bemcgarvey/SAMduino/firmware/FullDemo/firmware/src/config/default/default.mhc/project.yml

files:
- generatedChecksum: F58DB2348A0FCE945652B285010E5F8A
  logicalPath: FreeRTOS/Source
  name: FreeRTOS_tasks.c
  physicalPath: ../../third_party/rtos/FreeRTOS/Source
  security: NON_SECURE
  type: SOURCE
  userChecksum: F58DB2348A0FCE945652B285010E5F8A
- generatedChecksum: 3C13720844166A5D97CF4EAD9DDB9FE2
  logicalPath: ''
  name: app.c
  physicalPath: ../..
  security: NON_SECURE
  type: SOURCE
  userChecksum: 3C13720844166A5D97CF4EAD9DDB9FE2
- generatedChecksum: 8ACE0DEBD82F6829438A4674565451FB
  logicalPath: FreeRTOS/Source
  name: croutine.c
  physicalPath: ../../third_party/rtos/FreeRTOS/Source
  security: NON_SECURE
  type: SOURCE
  userChecksum: 8ACE0DEBD82F6829438A4674565451FB
- generatedChecksum: EA052CFEAD3E59E304995DACA53CE9B6
  logicalPath: config/default/driver/sst26
  name: drv_sst26.c
  physicalPath: driver/sst26/src
  security: NON_SECURE
  type: SOURCE
  userChecksum: EA052CFEAD3E59E304995DACA53CE9B6
- generatedChecksum: 680300EC1B71F449C4265A35B9ECA1BF
  logicalPath: config/default/driver/usb/usbhsv1/src
  name: drv_usbhsv1.c
  physicalPath: driver/usb/usbhsv1/src
  security: NON_SECURE
  type: SOURCE
  userChecksum: 680300EC1B71F449C4265A35B9ECA1BF
- generatedChecksum: 33A4AF962D182E0E51963CD431EE5B25
  logicalPath: config/default/driver/usb/usbhsv1/src
  name: drv_usbhsv1_device.c
  physicalPath: driver/usb/usbhsv1/src
  security: NON_SECURE
  type: SOURCE
  userChecksum: 33A4AF962D182E0E51963CD431EE5B25
- generatedChecksum: B3B5445B14BD9B6A35F1C5B995C9BBF7
  logicalPath: FreeRTOS/Source
  name: event_groups.c
  physicalPath: ../../third_party/rtos/FreeRTOS/Source
  security: NON_SECURE
  type: SOURCE
  userChecksum: B3B5445B14BD9B6A35F1C5B995C9BBF7
- generatedChecksum: 6069C4FD56993BDA3B1FC223DD5BAA4A
  logicalPath: config/default
  name: exceptions.c
  physicalPath: ''
  security: NON_SECURE
  type: SOURCE
  userChecksum: 6069C4FD56993BDA3B1FC223DD5BAA4A
- generatedChecksum: B7DBFD6F500AAD4713403E985EB18EAE
  logicalPath: config/default
  name: freertos_hooks.c
  physicalPath: ''
  security: NON_SECURE
  type: SOURCE
  userChecksum: B7DBFD6F500AAD4713403E985EB18EAE
- generatedChecksum: 972E955D94A63BA89BF6ABD6AADB1023
  logicalPath: FreeRTOS/Source/portable/MemMang
  name: heap_1.c
  physicalPath: ../../third_party/rtos/FreeRTOS/Source/portable/MemMang
  security: NON_SECURE
  type: SOURCE
  userChecksum: 972E955D94A63BA89BF6ABD6AADB1023
- generatedChecksum: 76F34BFBB493FA46B344390C7CF3CD15
  logicalPath: config/default
  name: initialization.c
  physicalPath: ''
  security: NON_SECURE
  type: SOURCE
  userChecksum: AD14C167BFB01463832A4C5FFC92C627
- generatedChecksum: BDF1F360A3F8C5AD9AE4D64B657A1878
  logicalPath: config/default
  name: interrupts.c
  physicalPath: ''
  security: NON_SECURE
  type: SOURCE
  userChecksum: BDF1F360A3F8C5AD9AE4D64B657A1878
- generatedChecksum: 6513F2461B8F476B68CA73906086047F
  logicalPath: config/default
  name: libc_syscalls.c
  physicalPath: ''
  security: NON_SECURE
  type: SOURCE
  userChecksum: 6513F2461B8F476B68CA73906086047F
- generatedChecksum: 3FEE521CEF14928AE38E7FA9BF6D75E6
  logicalPath: FreeRTOS/Source
  name: list.c
  physicalPath: ../../third_party/rtos/FreeRTOS/Source
  security: NON_SECURE
  type: SOURCE
  userChecksum: 3FEE521CEF14928AE38E7FA9BF6D75E6
- generatedChecksum: null
  logicalPath: ''
  name: main.c
  physicalPath: ../..
  security: NON_SECURE
  type: SOURCE
  userChecksum: null
- generatedChecksum: 8FDD6248506F28B32C4F5FD9AA0D9C6F
  logicalPath: config/default/osal
  name: osal_freertos.c
  physicalPath: osal
  security: NON_SECURE
  type: SOURCE
  userChecksum: 8FDD6248506F28B32C4F5FD9AA0D9C6F
- generatedChecksum: 706B0D62C31518F05ECE479F341C0C4A
  logicalPath: config/default/peripheral/afec
  name: plib_afec0.c
  physicalPath: peripheral/afec
  security: NON_SECURE
  type: SOURCE
  userChecksum: 706B0D62C31518F05ECE479F341C0C4A
- generatedChecksum: CCAA3BBC352DB66DF3CFBB76D3ADD2E2
  logicalPath: config/default/peripheral/clk
  name: plib_clk.c
  physicalPath: peripheral/clk
  security: NON_SECURE
  type: SOURCE
  userChecksum: CCAA3BBC352DB66DF3CFBB76D3ADD2E2
- generatedChecksum: 0B346F78158581AC40B9AC5F314CCE8B
  logicalPath: config/default/peripheral/dacc
  name: plib_dacc.c
  physicalPath: peripheral/dacc
  security: NON_SECURE
  type: SOURCE
  userChecksum: 0B346F78158581AC40B9AC5F314CCE8B
- generatedChecksum: D23DF612DB8267EDD9F5F3A463A02DB2
  logicalPath: config/default/peripheral/efc
  name: plib_efc.c
  physicalPath: peripheral/efc
  security: NON_SECURE
  type: SOURCE
  userChecksum: D23DF612DB8267EDD9F5F3A463A02DB2
- generatedChecksum: ED0FB91129ED2FAB77A9B83BCA98BB56
  logicalPath: config/default/peripheral/mcan
  name: plib_mcan1.c
  physicalPath: peripheral/mcan
  security: NON_SECURE
  type: SOURCE
  userChecksum: 1BCA5DFF8679503FCB69D2AA16217BDE
- generatedChecksum: 491997C3DCC743A5F66EBE18F705C9AF
  logicalPath: config/default/peripheral/mpu
  name: plib_mpu.c
  physicalPath: peripheral/mpu
  security: NON_SECURE
  type: SOURCE
  userChecksum: 491997C3DCC743A5F66EBE18F705C9AF
- generatedChecksum: 37F79C56E4B0579F6756EA357A5D6681
  logicalPath: config/default/peripheral/nvic
  name: plib_nvic.c
  physicalPath: peripheral/nvic
  security: NON_SECURE
  type: SOURCE
  userChecksum: 2B41430E0F8341E7698B5F92560EFE35
- generatedChecksum: AECA335D842D380909F5F2B9B9303612
  logicalPath: config/default/peripheral/pio
  name: plib_pio.c
  physicalPath: peripheral/pio
  security: NON_SECURE
  type: SOURCE
  userChecksum: AECA335D842D380909F5F2B9B9303612
- generatedChecksum: D54BE86FE71C530355BA300B4662D361
  logicalPath: config/default/peripheral/pwm
  name: plib_pwm0.c
  physicalPath: peripheral/pwm
  security: NON_SECURE
  type: SOURCE
  userChecksum: D54BE86FE71C530355BA300B4662D361
- generatedChecksum: 164CDE8DEA8E52ED78CD9E179EDDE260
  logicalPath: config/default/peripheral/qspi
  name: plib_qspi.c
  physicalPath: peripheral/qspi
  security: NON_SECURE
  type: SOURCE
  userChecksum: 164CDE8DEA8E52ED78CD9E179EDDE260
- generatedChecksum: 68F6A46E5DB2303BD0B1DC03F3436C98
  logicalPath: config/default/peripheral/rtc
  name: plib_rtc.c
  physicalPath: peripheral/rtc
  security: NON_SECURE
  type: SOURCE
  userChecksum: 68F6A46E5DB2303BD0B1DC03F3436C98
- generatedChecksum: B09ED1072864A1FCF957C698795DD7BD
  logicalPath: config/default/peripheral/tc
  name: plib_tc0.c
  physicalPath: peripheral/tc
  security: NON_SECURE
  type: SOURCE
  userChecksum: B09ED1072864A1FCF957C698795DD7BD
- generatedChecksum: 037AFDA32620C47534016E979C15AF5C
  logicalPath: config/default/peripheral/tc
  name: plib_tc1.c
  physicalPath: peripheral/tc
  security: NON_SECURE
  type: SOURCE
  userChecksum: 037AFDA32620C47534016E979C15AF5C
- generatedChecksum: 1DE96220F35A04CB1742747EFEA865BD
  logicalPath: config/default/peripheral/trng
  name: plib_trng.c
  physicalPath: peripheral/trng
  security: NON_SECURE
  type: SOURCE
  userChecksum: 1DE96220F35A04CB1742747EFEA865BD
- generatedChecksum: AD9E5D8957ADDF3C5B579114051BE96B
  logicalPath: config/default/peripheral/twihs/master
  name: plib_twihs0_master.c
  physicalPath: peripheral/twihs/master
  security: NON_SECURE
  type: SOURCE
  userChecksum: AD9E5D8957ADDF3C5B579114051BE96B
- generatedChecksum: CBEC3B1A0CD099BE51536D94DED55A0F
  logicalPath: config/default/peripheral/uart
  name: plib_uart0.c
  physicalPath: peripheral/uart
  security: NON_SECURE
  type: SOURCE
  userChecksum: 4709090D31EC54B2A1883D1C04EC0574
- generatedChecksum: A44EAFDF7F180C2C05A0AE0AEB3FB80C
  logicalPath: FreeRTOS/Source/portable/GCC/SAM/CM7
  name: port.c
  physicalPath: ../../third_party/rtos/FreeRTOS/Source/portable/GCC/SAM/CM7
  security: NON_SECURE
  type: SOURCE
  userChecksum: A44EAFDF7F180C2C05A0AE0AEB3FB80C
- generatedChecksum: 09041728D74A4E3A32C7D4EAA96C4EE7
  logicalPath: FreeRTOS/Source
  name: queue.c
  physicalPath: ../../third_party/rtos/FreeRTOS/Source
  security: NON_SECURE
  type: SOURCE
  userChecksum: 09041728D74A4E3A32C7D4EAA96C4EE7
- generatedChecksum: F199C711F99DEF2498D1F664873F2B12
  logicalPath: config/default
  name: startup_xc32.c
  physicalPath: ''
  security: NON_SECURE
  type: SOURCE
  userChecksum: F199C711F99DEF2498D1F664873F2B12
- generatedChecksum: D6CF30BDCE1A813D9ACF3905EBD6A871
  logicalPath: FreeRTOS/Source
  name: stream_buffer.c
  physicalPath: ../../third_party/rtos/FreeRTOS/Source
  security: NON_SECURE
  type: SOURCE
  userChecksum: D6CF30BDCE1A813D9ACF3905EBD6A871
- generatedChecksum: 9063CE23C03357B7F90CA6887D4BCAF9
  logicalPath: config/default/system/cache
  name: sys_cache.c
  physicalPath: system/cache
  security: NON_SECURE
  type: SOURCE
  userChecksum: 9063CE23C03357B7F90CA6887D4BCAF9
- generatedChecksum: 02C3C1B519E59992810626BB6098CF56
  logicalPath: config/default/system/int
  name: sys_int.c
  physicalPath: system/int/src
  security: NON_SECURE
  type: SOURCE
  userChecksum: 02C3C1B519E59992810626BB6098CF56
- generatedChecksum: 83BDE663A1AAB20C9E52263F22E2ED3C
  logicalPath: config/default/system/time
  name: sys_time.c
  physicalPath: system/time/src
  security: NON_SECURE
  type: SOURCE
  userChecksum: 83BDE663A1AAB20C9E52263F22E2ED3C
- generatedChecksum: C0B55E4D4726999758344B4532A6EF5F
  logicalPath: config/default
  name: tasks.c
  physicalPath: ''
  security: NON_SECURE
  type: SOURCE
  userChecksum: 2D95749151AAFEBDD75F7073DBA08B05
- generatedChecksum: F1B86F6E1527FD59A8713B67564F2898
  logicalPath: FreeRTOS/Source
  name: timers.c
  physicalPath: ../../third_party/rtos/FreeRTOS/Source
  security: NON_SECURE
  type: SOURCE
  userChecksum: F1B86F6E1527FD59A8713B67564F2898
- generatedChecksum: BCCEF5B801FFD0CF22D0B454D2F25F1F
  logicalPath: config/default/usb/src
  name: usb_device.c
  physicalPath: usb/src
  security: NON_SECURE
  type: SOURCE
  userChecksum: BCCEF5B801FFD0CF22D0B454D2F25F1F
- generatedChecksum: B8D87B6533E2CE239E9EEB8486DF6996
  logicalPath: config/default/usb/src
  name: usb_device_hid.c
  physicalPath: usb/src
  security: NON_SECURE
  type: SOURCE
  userChecksum: B8D87B6533E2CE239E9EEB8486DF6996
- generatedChecksum: A4132D906937F33AE060B60BD472DB28
  logicalPath: config/default
  name: usb_device_init_data.c
  physicalPath: ''
  security: NON_SECURE
  type: SOURCE
  userChecksum: A4132D906937F33AE060B60BD472DB28
- generatedChecksum: A49786F231DE2706850DA13580EF4BB5
  logicalPath: config/default/stdio
  name: xc32_monitor.c
  physicalPath: stdio
  security: NON_SECURE
  type: SOURCE
  userChecksum: A49786F231DE2706850DA13580EF4BB5
- generatedChecksum: AF3A8D8AA610E7DFD3E38DDAC5E42074
  logicalPath: FreeRTOS/Source/include
  name: FreeRTOS.h
  physicalPath: ../../third_party/rtos/FreeRTOS/Source/include
  security: NON_SECURE
  type: HEADER
  userChecksum: AF3A8D8AA610E7DFD3E38DDAC5E42074
- generatedChecksum: E27174ED5C5A94F058706A7328D236D1
  logicalPath: config/default
  name: FreeRTOSConfig.h
  physicalPath: ''
  security: NON_SECURE
  type: HEADER
  userChecksum: E27174ED5C5A94F058706A7328D236D1
- generatedChecksum: 641EA28F78A04E01087965FE462B3419
  logicalPath: packs/ATSAMV71N21B_DFP/component
  name: acc.h
  physicalPath: ../../packs/ATSAMV71N21B_DFP/component
  security: NON_SECURE
  type: HEADER
  userChecksum: 641EA28F78A04E01087965FE462B3419
- generatedChecksum: BD7A3CD9142949784DD0FACA7CF75DAB
  logicalPath: packs/ATSAMV71N21B_DFP/instance
  name: acc.h
  physicalPath: ../../packs/ATSAMV71N21B_DFP/instance
  security: NON_SECURE
  type: HEADER
  userChecksum: BD7A3CD9142949784DD0FACA7CF75DAB
- generatedChecksum: 13E46AF74F09663589ACA838901BFAF2
  logicalPath: packs/ATSAMV71N21B_DFP/component
  name: aes.h
  physicalPath: ../../packs/ATSAMV71N21B_DFP/component
  security: NON_SECURE
  type: HEADER
  userChecksum: 13E46AF74F09663589ACA838901BFAF2
- generatedChecksum: D2214DF5256459D58AC0CC427DCD4928
  logicalPath: packs/ATSAMV71N21B_DFP/instance
  name: aes.h
  physicalPath: ../../packs/ATSAMV71N21B_DFP/instance
  security: NON_SECURE
  type: HEADER
  userChecksum: D2214DF5256459D58AC0CC427DCD4928
- generatedChecksum: 575A75C7E277CFF37378DFF9AD14CB6B
  logicalPath: packs/ATSAMV71N21B_DFP/component
  name: afec.h
  physicalPath: ../../packs/ATSAMV71N21B_DFP/component
  security: NON_SECURE
  type: HEADER
  userChecksum: 575A75C7E277CFF37378DFF9AD14CB6B
- generatedChecksum: DF405E511218B8338C0BA361FF83B66B
  logicalPath: packs/ATSAMV71N21B_DFP/instance
  name: afec0.h
  physicalPath: ../../packs/ATSAMV71N21B_DFP/instance
  security: NON_SECURE
  type: HEADER
  userChecksum: DF405E511218B8338C0BA361FF83B66B
- generatedChecksum: 625DFAF8957213A83B43E401F0F9B76D
  logicalPath: packs/ATSAMV71N21B_DFP/instance
  name: afec1.h
  physicalPath: ../../packs/ATSAMV71N21B_DFP/instance
  security: NON_SECURE
  type: HEADER
  userChecksum: 625DFAF8957213A83B43E401F0F9B76D
- generatedChecksum: 452F7AB915EEA4B1529959D0FF80C3F7
  logicalPath: ''
  name: app.h
  physicalPath: ../..
  security: NON_SECURE
  type: HEADER
  userChecksum: 452F7AB915EEA4B1529959D0FF80C3F7
- generatedChecksum: 14F1AD56D242EFD0AF76849C6ADFECC4
  logicalPath: packs/CMSIS/CMSIS/Core/Include
  name: cachel1_armv7.h
  physicalPath: ../../packs/CMSIS/CMSIS/Core/Include
  security: NON_SECURE
  type: HEADER
  userChecksum: 14F1AD56D242EFD0AF76849C6ADFECC4
- generatedChecksum: 5301C9C25BD211AAE67DE2A86B9947D5
  logicalPath: packs/ATSAMV71N21B_DFP/component
  name: chipid.h
  physicalPath: ../../packs/ATSAMV71N21B_DFP/component
  security: NON_SECURE
  type: HEADER
  userChecksum: 5301C9C25BD211AAE67DE2A86B9947D5
- generatedChecksum: E8DC7A2DE3BF0C567101B46C67D262E8
  logicalPath: packs/ATSAMV71N21B_DFP/instance
  name: chipid.h
  physicalPath: ../../packs/ATSAMV71N21B_DFP/instance
  security: NON_SECURE
  type: HEADER
  userChecksum: E8DC7A2DE3BF0C567101B46C67D262E8
- generatedChecksum: B79C08E0901948AD04D944B4BCE1B60D
  logicalPath: packs/CMSIS/CMSIS/Core/Include
  name: cmsis_armcc.h
  physicalPath: ../../packs/CMSIS/CMSIS/Core/Include
  security: NON_SECURE
  type: HEADER
  userChecksum: B79C08E0901948AD04D944B4BCE1B60D
- generatedChecksum: 6B4E2EBA8708D9E04E6136F29460ACB9
  logicalPath: packs/CMSIS/CMSIS/Core/Include
  name: cmsis_armclang.h
  physicalPath: ../../packs/CMSIS/CMSIS/Core/Include
  security: NON_SECURE
  type: HEADER
  userChecksum: 6B4E2EBA8708D9E04E6136F29460ACB9
- generatedChecksum: 415E22EBE7A3BACE87240A7F16492C46
  logicalPath: packs/CMSIS/CMSIS/Core/Include
  name: cmsis_armclang_ltm.h
  physicalPath: ../../packs/CMSIS/CMSIS/Core/Include
  security: NON_SECURE
  type: HEADER
  userChecksum: 415E22EBE7A3BACE87240A7F16492C46
- generatedChecksum: 60385A5C6C9882B5D30709A1F6EAEC35
  logicalPath: packs/CMSIS/CMSIS/Core/Include
  name: cmsis_compiler.h
  physicalPath: ../../packs/CMSIS/CMSIS/Core/Include
  security: NON_SECURE
  type: HEADER
  userChecksum: 60385A5C6C9882B5D30709A1F6EAEC35
- generatedChecksum: 4DC978B079559EB044AFD32A57768238
  logicalPath: packs/CMSIS/CMSIS/Core/Include
  name: cmsis_gcc.h
  physicalPath: ../../packs/CMSIS/CMSIS/Core/Include
  security: NON_SECURE
  type: HEADER
  userChecksum: 4DC978B079559EB044AFD32A57768238
- generatedChecksum: 11521476050CAC6C1F3A91A5BB5DBB9A
  logicalPath: packs/CMSIS/CMSIS/Core/Include
  name: cmsis_iccarm.h
  physicalPath: ../../packs/CMSIS/CMSIS/Core/Include
  security: NON_SECURE
  type: HEADER
  userChecksum: 11521476050CAC6C1F3A91A5BB5DBB9A
- generatedChecksum: 52F91AC0727F2311EDA0E3BAA7719A9F
  logicalPath: packs/CMSIS/CMSIS/Core/Include
  name: cmsis_version.h
  physicalPath: ../../packs/CMSIS/CMSIS/Core/Include
  security: NON_SECURE
  type: HEADER
  userChecksum: 52F91AC0727F2311EDA0E3BAA7719A9F
- generatedChecksum: 9A726A831264066FA2C452F76139EB81
  logicalPath: config/default
  name: configuration.h
  physicalPath: ''
  security: NON_SECURE
  type: HEADER
  userChecksum: 9A726A831264066FA2C452F76139EB81
- generatedChecksum: 948CEA542F04017255B040816F368DF8
  logicalPath: packs/CMSIS/CMSIS/Core/Include
  name: core_cm7.h
  physicalPath: ../../packs/CMSIS/CMSIS/Core/Include
  security: NON_SECURE
  type: HEADER
  userChecksum: 948CEA542F04017255B040816F368DF8
- generatedChecksum: 48B661D8C967C6BC397001F10FB43D1D
  logicalPath: FreeRTOS/Source/include
  name: croutine.h
  physicalPath: ../../third_party/rtos/FreeRTOS/Source/include
  security: NON_SECURE
  type: HEADER
  userChecksum: 48B661D8C967C6BC397001F10FB43D1D
- generatedChecksum: 77A49F3B49CF83DE4BC85C743884DBE7
  logicalPath: packs/ATSAMV71N21B_DFP/component
  name: dacc.h
  physicalPath: ../../packs/ATSAMV71N21B_DFP/component
  security: NON_SECURE
  type: HEADER
  userChecksum: 77A49F3B49CF83DE4BC85C743884DBE7
- generatedChecksum: B424335B8194FB845DFEE348D5ACCDA0
  logicalPath: packs/ATSAMV71N21B_DFP/instance
  name: dacc.h
  physicalPath: ../../packs/ATSAMV71N21B_DFP/instance
  security: NON_SECURE
  type: HEADER
  userChecksum: B424335B8194FB845DFEE348D5ACCDA0
- generatedChecksum: 0937E96F6D82B796AB78FA21C931D242
  logicalPath: config/default
  name: definitions.h
  physicalPath: ''
  security: NON_SECURE
  type: HEADER
  userChecksum: 339B1036D00CECD3B08990FD4EFA4955
- generatedChecksum: 1EA4EDD5EA90F43EC407DE32441159A9
  logicalPath: FreeRTOS/Source/include
  name: deprecated_definitions.h
  physicalPath: ../../third_party/rtos/FreeRTOS/Source/include
  security: NON_SECURE
  type: HEADER
  userChecksum: 1EA4EDD5EA90F43EC407DE32441159A9
- generatedChecksum: 3AF237725C26767B231B9DF6D83C3920
  logicalPath: config/default
  name: device.h
  physicalPath: ''
  security: NON_SECURE
  type: HEADER
  userChecksum: 3AF237725C26767B231B9DF6D83C3920
- generatedChecksum: 9FD18F0D30B89945CC141BA0DE2ABE90
  logicalPath: config/default
  name: device_cache.h
  physicalPath: ''
  security: NON_SECURE
  type: HEADER
  userChecksum: 9FD18F0D30B89945CC141BA0DE2ABE90
- generatedChecksum: D4DF9B77C2FAD66A278B6EFC86F5D1D4
  logicalPath: config/default
  name: device_vectors.h
  physicalPath: ''
  security: NON_SECURE
  type: HEADER
  userChecksum: D4DF9B77C2FAD66A278B6EFC86F5D1D4
- generatedChecksum: 1D2094DFA60F847FFD4E8153B6E78027
  logicalPath: config/default/driver
  name: driver.h
  physicalPath: driver
  security: NON_SECURE
  type: HEADER
  userChecksum: 1D2094DFA60F847FFD4E8153B6E78027
- generatedChecksum: CC7DFCC51CD25171A3E400E18969354F
  logicalPath: config/default/driver
  name: driver_common.h
  physicalPath: driver
  security: NON_SECURE
  type: HEADER
  userChecksum: CC7DFCC51CD25171A3E400E18969354F
- generatedChecksum: 8EAE086FFBCC60C4343BAA26620B1204
  logicalPath: config/default/driver/sst26
  name: drv_sst26.h
  physicalPath: driver/sst26
  security: NON_SECURE
  type: HEADER
  userChecksum: 8EAE086FFBCC60C4343BAA26620B1204
- generatedChecksum: 39820E4FEA4DC1598585895FC87D27CD
  logicalPath: config/default/driver/sst26
  name: drv_sst26_definitions.h
  physicalPath: driver/sst26
  security: NON_SECURE
  type: HEADER
  userChecksum: 39820E4FEA4DC1598585895FC87D27CD
- generatedChecksum: D0F58EA0E69F1EC3040F9EB3C64B9737
  logicalPath: config/default/driver/sst26
  name: drv_sst26_local.h
  physicalPath: driver/sst26/src
  security: NON_SECURE
  type: HEADER
  userChecksum: D0F58EA0E69F1EC3040F9EB3C64B9737
- generatedChecksum: DF147276AE56CA76E3E9BEB8447620AB
  logicalPath: config/default/driver/usb
  name: drv_usb.h
  physicalPath: driver/usb
  security: NON_SECURE
  type: HEADER
  userChecksum: DF147276AE56CA76E3E9BEB8447620AB
- generatedChecksum: A8072403A5346EF85CDFD4EF996C0826
  logicalPath: config/default/driver/usb
  name: drv_usb_external_dependencies.h
  physicalPath: driver/usb
  security: NON_SECURE
  type: HEADER
  userChecksum: A8072403A5346EF85CDFD4EF996C0826
- generatedChecksum: 6F8CC07CA11B3FD9B105D2AFE9FE3A28
  logicalPath: config/default/driver/usb/usbhsv1
  name: drv_usbhsv1.h
  physicalPath: driver/usb/usbhsv1
  security: NON_SECURE
  type: HEADER
  userChecksum: 6F8CC07CA11B3FD9B105D2AFE9FE3A28
- generatedChecksum: 2CDE0E6FF0A0FF3E14F743D08E064584
  logicalPath: config/default/driver/usb/usbhsv1/src
  name: drv_usbhsv1_local.h
  physicalPath: driver/usb/usbhsv1/src
  security: NON_SECURE
  type: HEADER
  userChecksum: 2CDE0E6FF0A0FF3E14F743D08E064584
- generatedChecksum: F4E8736C8A43D37DDC0F661D194AAF8A
  logicalPath: config/default/driver/usb/usbhsv1/src
  name: drv_usbhsv1_variant_mapping.h
  physicalPath: driver/usb/usbhsv1/src
  security: NON_SECURE
  type: HEADER
  userChecksum: F4E8736C8A43D37DDC0F661D194AAF8A
- generatedChecksum: B47AFDC4BCD83F20528136ED659BF8A7
  logicalPath: packs/ATSAMV71N21B_DFP/component
  name: efc.h
  physicalPath: ../../packs/ATSAMV71N21B_DFP/component
  security: NON_SECURE
  type: HEADER
  userChecksum: B47AFDC4BCD83F20528136ED659BF8A7
- generatedChecksum: F58764DB84FAE55CC7A088BD8D11B6B0
  logicalPath: packs/ATSAMV71N21B_DFP/instance
  name: efc.h
  physicalPath: ../../packs/ATSAMV71N21B_DFP/instance
  security: NON_SECURE
  type: HEADER
  userChecksum: F58764DB84FAE55CC7A088BD8D11B6B0
- generatedChecksum: B1D1D455E111FA70C46AD40562D78CE2
  logicalPath: FreeRTOS/Source/include
  name: event_groups.h
  physicalPath: ../../third_party/rtos/FreeRTOS/Source/include
  security: NON_SECURE
  type: HEADER
  userChecksum: B1D1D455E111FA70C46AD40562D78CE2
- generatedChecksum: D096C79BD5B10448F69434F981148958
  logicalPath: packs/ATSAMV71N21B_DFP/component
  name: fuses.h
  physicalPath: ../../packs/ATSAMV71N21B_DFP/component
  security: NON_SECURE
  type: HEADER
  userChecksum: D096C79BD5B10448F69434F981148958
- generatedChecksum: 6196AAD2443EBF9A33B090521BB66E31
  logicalPath: packs/ATSAMV71N21B_DFP/instance
  name: fuses.h
  physicalPath: ../../packs/ATSAMV71N21B_DFP/instance
  security: NON_SECURE
  type: HEADER
  userChecksum: 6196AAD2443EBF9A33B090521BB66E31
- generatedChecksum: 3A278C9A5AC8A7F5E0BF43C2E8684B99
  logicalPath: packs/ATSAMV71N21B_DFP/component
  name: gmac.h
  physicalPath: ../../packs/ATSAMV71N21B_DFP/component
  security: NON_SECURE
  type: HEADER
  userChecksum: 3A278C9A5AC8A7F5E0BF43C2E8684B99
- generatedChecksum: AC8CD1C278A6970BE22BC4713C996B1A
  logicalPath: packs/ATSAMV71N21B_DFP/instance
  name: gmac.h
  physicalPath: ../../packs/ATSAMV71N21B_DFP/instance
  security: NON_SECURE
  type: HEADER
  userChecksum: AC8CD1C278A6970BE22BC4713C996B1A
- generatedChecksum: 44E1901A7BCCE940265E56A45539C104
  logicalPath: packs/ATSAMV71N21B_DFP/component
  name: gpbr.h
  physicalPath: ../../packs/ATSAMV71N21B_DFP/component
  security: NON_SECURE
  type: HEADER
  userChecksum: 44E1901A7BCCE940265E56A45539C104
- generatedChecksum: F22BD38BCE680EF3E1753C45B2FF0F49
  logicalPath: packs/ATSAMV71N21B_DFP/instance
  name: gpbr.h
  physicalPath: ../../packs/ATSAMV71N21B_DFP/instance
  security: NON_SECURE
  type: HEADER
  userChecksum: F22BD38BCE680EF3E1753C45B2FF0F49
- generatedChecksum: 75BC83F8498D9FD73140398FF1FB5464
  logicalPath: packs/ATSAMV71N21B_DFP/component
  name: hsmci.h
  physicalPath: ../../packs/ATSAMV71N21B_DFP/component
  security: NON_SECURE
  type: HEADER
  userChecksum: 75BC83F8498D9FD73140398FF1FB5464
- generatedChecksum: F605DF4C229F51B0A776DD0DCE24CD17
  logicalPath: packs/ATSAMV71N21B_DFP/instance
  name: hsmci.h
  physicalPath: ../../packs/ATSAMV71N21B_DFP/instance
  security: NON_SECURE
  type: HEADER
  userChecksum: F605DF4C229F51B0A776DD0DCE24CD17
- generatedChecksum: 9101EA54B77285D24B50846720989AD6
  logicalPath: packs/ATSAMV71N21B_DFP/component
  name: i2sc.h
  physicalPath: ../../packs/ATSAMV71N21B_DFP/component
  security: NON_SECURE
  type: HEADER
  userChecksum: 9101EA54B77285D24B50846720989AD6
- generatedChecksum: D9352E1B4215C5B99FA7260B241F93BE
  logicalPath: packs/ATSAMV71N21B_DFP/instance
  name: i2sc0.h
  physicalPath: ../../packs/ATSAMV71N21B_DFP/instance
  security: NON_SECURE
  type: HEADER
  userChecksum: D9352E1B4215C5B99FA7260B241F93BE
- generatedChecksum: BF3C5E42D7E3B726501C0C478FF598B2
  logicalPath: packs/ATSAMV71N21B_DFP/instance
  name: i2sc1.h
  physicalPath: ../../packs/ATSAMV71N21B_DFP/instance
  security: NON_SECURE
  type: HEADER
  userChecksum: BF3C5E42D7E3B726501C0C478FF598B2
- generatedChecksum: 3568D7C8BF5EEAF9D39EC8DACA1CB006
  logicalPath: packs/ATSAMV71N21B_DFP/component
  name: icm.h
  physicalPath: ../../packs/ATSAMV71N21B_DFP/component
  security: NON_SECURE
  type: HEADER
  userChecksum: 3568D7C8BF5EEAF9D39EC8DACA1CB006
- generatedChecksum: 48C1CAD197BD52C6E48A6C4BA57521CE
  logicalPath: packs/ATSAMV71N21B_DFP/instance
  name: icm.h
  physicalPath: ../../packs/ATSAMV71N21B_DFP/instance
  security: NON_SECURE
  type: HEADER
  userChecksum: 48C1CAD197BD52C6E48A6C4BA57521CE
- generatedChecksum: BF0BB7A78285537ABAE9887FD568CC4E
  logicalPath: config/default
  name: interrupts.h
  physicalPath: ''
  security: NON_SECURE
  type: HEADER
  userChecksum: 8848DE215873122365F7A15C021CE160
- generatedChecksum: 0EBBEFA82D9C3EDCC36616B0EB43352A
  logicalPath: packs/ATSAMV71N21B_DFP/component
  name: isi.h
  physicalPath: ../../packs/ATSAMV71N21B_DFP/component
  security: NON_SECURE
  type: HEADER
  userChecksum: 0EBBEFA82D9C3EDCC36616B0EB43352A
- generatedChecksum: 3CB7388F5295AF7EBE9703E56E811824
  logicalPath: packs/ATSAMV71N21B_DFP/instance
  name: isi.h
  physicalPath: ../../packs/ATSAMV71N21B_DFP/instance
  security: NON_SECURE
  type: HEADER
  userChecksum: 3CB7388F5295AF7EBE9703E56E811824
- generatedChecksum: FE17D325A06479D956285C5438994B83
  logicalPath: FreeRTOS/Source/include
  name: list.h
  physicalPath: ../../third_party/rtos/FreeRTOS/Source/include
  security: NON_SECURE
  type: HEADER
  userChecksum: FE17D325A06479D956285C5438994B83
- generatedChecksum: 4E113B7CD481442FD4E18D7AF4BD2033
  logicalPath: packs/ATSAMV71N21B_DFP/component
  name: matrix.h
  physicalPath: ../../packs/ATSAMV71N21B_DFP/component
  security: NON_SECURE
  type: HEADER
  userChecksum: 4E113B7CD481442FD4E18D7AF4BD2033
- generatedChecksum: 301DB7410B8AFB10DE5ABE5599F5E0FF
  logicalPath: packs/ATSAMV71N21B_DFP/instance
  name: matrix.h
  physicalPath: ../../packs/ATSAMV71N21B_DFP/instance
  security: NON_SECURE
  type: HEADER
  userChecksum: 301DB7410B8AFB10DE5ABE5599F5E0FF
- generatedChecksum: 7410E488D2931002E6C3EC1B3A714DCF
  logicalPath: packs/ATSAMV71N21B_DFP/component
  name: mcan.h
  physicalPath: ../../packs/ATSAMV71N21B_DFP/component
  security: NON_SECURE
  type: HEADER
  userChecksum: 7410E488D2931002E6C3EC1B3A714DCF
- generatedChecksum: F261619661DEF85432069C225D22E1F3
  logicalPath: packs/ATSAMV71N21B_DFP/instance
  name: mcan0.h
  physicalPath: ../../packs/ATSAMV71N21B_DFP/instance
  security: NON_SECURE
  type: HEADER
  userChecksum: F261619661DEF85432069C225D22E1F3
- generatedChecksum: 7D3D62342BF3F7EBB10EA52845608A80
  logicalPath: packs/ATSAMV71N21B_DFP/instance
  name: mcan1.h
  physicalPath: ../../packs/ATSAMV71N21B_DFP/instance
  security: NON_SECURE
  type: HEADER
  userChecksum: 7D3D62342BF3F7EBB10EA52845608A80
- generatedChecksum: DDE2C9D46642D120A0202AC851E1A777
  logicalPath: FreeRTOS/Source/include
  name: message_buffer.h
  physicalPath: ../../third_party/rtos/FreeRTOS/Source/include
  security: NON_SECURE
  type: HEADER
  userChecksum: DDE2C9D46642D120A0202AC851E1A777
- generatedChecksum: F5FCD557377E1329573379FB11471AD2
  logicalPath: packs/ATSAMV71N21B_DFP/component
  name: mlb.h
  physicalPath: ../../packs/ATSAMV71N21B_DFP/component
  security: NON_SECURE
  type: HEADER
  userChecksum: F5FCD557377E1329573379FB11471AD2
- generatedChecksum: 3E8CD5F73754B38F73AB65EEB1B80883
  logicalPath: packs/ATSAMV71N21B_DFP/instance
  name: mlb.h
  physicalPath: ../../packs/ATSAMV71N21B_DFP/instance
  security: NON_SECURE
  type: HEADER
  userChecksum: 3E8CD5F73754B38F73AB65EEB1B80883
- generatedChecksum: 47E760D36E42A7B436306A9CB4E72A0E
  logicalPath: packs/CMSIS/CMSIS/Core/Include
  name: mpu_armv7.h
  physicalPath: ../../packs/CMSIS/CMSIS/Core/Include
  security: NON_SECURE
  type: HEADER
  userChecksum: 47E760D36E42A7B436306A9CB4E72A0E
- generatedChecksum: 2D674B8B1FCF07504AF90FA5CE2F9A23
  logicalPath: FreeRTOS/Source/include
  name: mpu_prototypes.h
  physicalPath: ../../third_party/rtos/FreeRTOS/Source/include
  security: NON_SECURE
  type: HEADER
  userChecksum: 2D674B8B1FCF07504AF90FA5CE2F9A23
- generatedChecksum: 953D372D8F7991D4F86AD4ABD42AE4CE
  logicalPath: FreeRTOS/Source/include
  name: mpu_wrappers.h
  physicalPath: ../../third_party/rtos/FreeRTOS/Source/include
  security: NON_SECURE
  type: HEADER
  userChecksum: 953D372D8F7991D4F86AD4ABD42AE4CE
- generatedChecksum: F0AD88762263B7CB89B02AB4F5876059
  logicalPath: config/default/osal
  name: osal.h
  physicalPath: osal
  security: NON_SECURE
  type: HEADER
  userChecksum: F0AD88762263B7CB89B02AB4F5876059
- generatedChecksum: 167A43EFF8A31441EBF85AC77958A30B
  logicalPath: config/default/osal
  name: osal_definitions.h
  physicalPath: osal
  security: NON_SECURE
  type: HEADER
  userChecksum: 167A43EFF8A31441EBF85AC77958A30B
- generatedChecksum: 9D6F205ECFDB2028C5CF766B52B5B7B2
  logicalPath: config/default/osal
  name: osal_freertos.h
  physicalPath: osal
  security: NON_SECURE
  type: HEADER
  userChecksum: 9D6F205ECFDB2028C5CF766B52B5B7B2
- generatedChecksum: 5E7A3789371F782859CEBEA0FF3B3E1D
  logicalPath: packs/ATSAMV71N21B_DFP/component
  name: pio.h
  physicalPath: ../../packs/ATSAMV71N21B_DFP/component
  security: NON_SECURE
  type: HEADER
  userChecksum: 5E7A3789371F782859CEBEA0FF3B3E1D
- generatedChecksum: 1500054F5C3BDE6ACE0826E6D7039127
  logicalPath: packs/ATSAMV71N21B_DFP/instance
  name: pioa.h
  physicalPath: ../../packs/ATSAMV71N21B_DFP/instance
  security: NON_SECURE
  type: HEADER
  userChecksum: 1500054F5C3BDE6ACE0826E6D7039127
- generatedChecksum: 1CF36E73DB1D6CE63AA64CAE8E9B317A
  logicalPath: packs/ATSAMV71N21B_DFP/instance
  name: piob.h
  physicalPath: ../../packs/ATSAMV71N21B_DFP/instance
  security: NON_SECURE
  type: HEADER
  userChecksum: 1CF36E73DB1D6CE63AA64CAE8E9B317A
- generatedChecksum: A46DDB145F7B388F783788F0481E0C40
  logicalPath: packs/ATSAMV71N21B_DFP/instance
  name: pioc.h
  physicalPath: ../../packs/ATSAMV71N21B_DFP/instance
  security: NON_SECURE
  type: HEADER
  userChecksum: A46DDB145F7B388F783788F0481E0C40
- generatedChecksum: 90E9CA351134066B6AF94A5A93CC4E3B
  logicalPath: packs/ATSAMV71N21B_DFP/instance
  name: piod.h
  physicalPath: ../../packs/ATSAMV71N21B_DFP/instance
  security: NON_SECURE
  type: HEADER
  userChecksum: 90E9CA351134066B6AF94A5A93CC4E3B
- generatedChecksum: AF1FC4BC990E73FAC9D75F3E58DB9DF2
  logicalPath: packs/ATSAMV71N21B_DFP/instance
  name: pioe.h
  physicalPath: ../../packs/ATSAMV71N21B_DFP/instance
  security: NON_SECURE
  type: HEADER
  userChecksum: AF1FC4BC990E73FAC9D75F3E58DB9DF2
- generatedChecksum: 327C1089B717F817C174C2F3FA44E1A1
  logicalPath: config/default/peripheral/afec
  name: plib_afec0.h
  physicalPath: peripheral/afec
  security: NON_SECURE
  type: HEADER
  userChecksum: 327C1089B717F817C174C2F3FA44E1A1
- generatedChecksum: E1F22172394877E78C6A32ACC21A00BE
  logicalPath: config/default/peripheral/afec
  name: plib_afec_common.h
  physicalPath: peripheral/afec
  security: NON_SECURE
  type: HEADER
  userChecksum: E1F22172394877E78C6A32ACC21A00BE
- generatedChecksum: BFDB10EBEF4DBDE66563BA7DD136A98F
  logicalPath: config/default/peripheral/clk
  name: plib_clk.h
  physicalPath: peripheral/clk
  security: NON_SECURE
  type: HEADER
  userChecksum: BFDB10EBEF4DBDE66563BA7DD136A98F
- generatedChecksum: F579237DA20C2E515A5AC366B38489E7
  logicalPath: config/default/peripheral/dacc
  name: plib_dacc.h
  physicalPath: peripheral/dacc
  security: NON_SECURE
  type: HEADER
  userChecksum: F579237DA20C2E515A5AC366B38489E7
- generatedChecksum: CD8125A18052720A72472D0F1DD6EC2B
  logicalPath: config/default/peripheral/dacc
  name: plib_dacc_common.h
  physicalPath: peripheral/dacc
  security: NON_SECURE
  type: HEADER
  userChecksum: CD8125A18052720A72472D0F1DD6EC2B
- generatedChecksum: 0ABDA5C4051B45BB0C8746712B766240
  logicalPath: config/default/peripheral/efc
  name: plib_efc.h
  physicalPath: peripheral/efc
  security: NON_SECURE
  type: HEADER
  userChecksum: 0ABDA5C4051B45BB0C8746712B766240
- generatedChecksum: 04977B5124BDA1625A4F7901463469AA
  logicalPath: config/default/peripheral/mcan
  name: plib_mcan1.h
  physicalPath: peripheral/mcan
  security: NON_SECURE
  type: HEADER
  userChecksum: 04977B5124BDA1625A4F7901463469AA
- generatedChecksum: 30C7DE721C75CF53A440475976FFA0DD
  logicalPath: config/default/peripheral/mcan
  name: plib_mcan_common.h
  physicalPath: peripheral/mcan
  security: NON_SECURE
  type: HEADER
  userChecksum: 30C7DE721C75CF53A440475976FFA0DD
- generatedChecksum: 6736D89FF27ACC5342105A1FCB2C5B13
  logicalPath: config/default/peripheral/mpu
  name: plib_mpu.h
  physicalPath: peripheral/mpu
  security: NON_SECURE
  type: HEADER
  userChecksum: 6736D89FF27ACC5342105A1FCB2C5B13
- generatedChecksum: E13B3C3F2096A36698DDC9B5BDE2E776
  logicalPath: config/default/peripheral/mpu
  name: plib_mpu_local.h
  physicalPath: peripheral/mpu
  security: NON_SECURE
  type: HEADER
  userChecksum: E13B3C3F2096A36698DDC9B5BDE2E776
- generatedChecksum: 55ECCC7FA71BD15B46EF80DC0515ED7A
  logicalPath: config/default/peripheral/nvic
  name: plib_nvic.h
  physicalPath: peripheral/nvic
  security: NON_SECURE
  type: HEADER
  userChecksum: 55ECCC7FA71BD15B46EF80DC0515ED7A
- generatedChecksum: 78A0AD8582A5DB127801BFE6F4B7F626
  logicalPath: config/default/peripheral/pio
  name: plib_pio.h
  physicalPath: peripheral/pio
  security: NON_SECURE
  type: HEADER
  userChecksum: 78A0AD8582A5DB127801BFE6F4B7F626
- generatedChecksum: AD4B052762D9DD83A0AFD7FDF3F6633E
  logicalPath: config/default/peripheral/pwm
  name: plib_pwm0.h
  physicalPath: peripheral/pwm
  security: NON_SECURE
  type: HEADER
  userChecksum: AD4B052762D9DD83A0AFD7FDF3F6633E
- generatedChecksum: E1F7C89AE3F4E8212824DB5B9A77E63E
  logicalPath: config/default/peripheral/pwm
  name: plib_pwm_common.h
  physicalPath: peripheral/pwm
  security: NON_SECURE
  type: HEADER
  userChecksum: E1F7C89AE3F4E8212824DB5B9A77E63E
- generatedChecksum: B7F8E9BB36B9F587A16CFABC3AAA95D4
  logicalPath: config/default/peripheral/qspi
  name: plib_qspi.h
  physicalPath: peripheral/qspi
  security: NON_SECURE
  type: HEADER
  userChecksum: B7F8E9BB36B9F587A16CFABC3AAA95D4
- generatedChecksum: 4C5986A0277E63F8568BDB343A280B17
  logicalPath: config/default/peripheral/qspi
  name: plib_qspi_common.h
  physicalPath: peripheral/qspi
  security: NON_SECURE
  type: HEADER
  userChecksum: 4C5986A0277E63F8568BDB343A280B17
- generatedChecksum: 621AE9009C9F785D735088FDD9252CDF
  logicalPath: config/default/peripheral/rtc
  name: plib_rtc.h
  physicalPath: peripheral/rtc
  security: NON_SECURE
  type: HEADER
  userChecksum: 621AE9009C9F785D735088FDD9252CDF
- generatedChecksum: 23DD6551AAD0E0BE65CAE99ECB44BD61
  logicalPath: config/default/peripheral/rtc
  name: plib_rtc_common.h
  physicalPath: peripheral/rtc
  security: NON_SECURE
  type: HEADER
  userChecksum: 23DD6551AAD0E0BE65CAE99ECB44BD61
- generatedChecksum: F952A04280324728AAE8A27EC09D2FF2
  logicalPath: config/default/peripheral/tc
  name: plib_tc0.h
  physicalPath: peripheral/tc
  security: NON_SECURE
  type: HEADER
  userChecksum: F952A04280324728AAE8A27EC09D2FF2
- generatedChecksum: DC0CC1475AD41EB14754670AEE4A0D2A
  logicalPath: config/default/peripheral/tc
  name: plib_tc1.h
  physicalPath: peripheral/tc
  security: NON_SECURE
  type: HEADER
  userChecksum: DC0CC1475AD41EB14754670AEE4A0D2A
- generatedChecksum: A2F276372C68B8EE16FB32AE5DF1BE37
  logicalPath: config/default/peripheral/tc
  name: plib_tc_common.h
  physicalPath: peripheral/tc
  security: NON_SECURE
  type: HEADER
  userChecksum: A2F276372C68B8EE16FB32AE5DF1BE37
- generatedChecksum: D3806C52C0B0050BA724D2F3F0357FC3
  logicalPath: config/default/peripheral/trng
  name: plib_trng.h
  physicalPath: peripheral/trng
  security: NON_SECURE
  type: HEADER
  userChecksum: D3806C52C0B0050BA724D2F3F0357FC3
- generatedChecksum: 165F1AE43FA1838644A54F43F1A0198D
  logicalPath: config/default/peripheral/twihs/master
  name: plib_twihs0_master.h
  physicalPath: peripheral/twihs/master
  security: NON_SECURE
  type: HEADER
  userChecksum: 165F1AE43FA1838644A54F43F1A0198D
- generatedChecksum: 5132029297BC9554EFA0EC40D3C0BC74
  logicalPath: config/default/peripheral/twihs/master
  name: plib_twihs_master_common.h
  physicalPath: peripheral/twihs/master
  security: NON_SECURE
  type: HEADER
  userChecksum: 5132029297BC9554EFA0EC40D3C0BC74
- generatedChecksum: 4B3E55A95240B58526FC2D8BFA561D2B
  logicalPath: config/default/peripheral/uart
  name: plib_uart0.h
  physicalPath: peripheral/uart
  security: NON_SECURE
  type: HEADER
  userChecksum: 4B3E55A95240B58526FC2D8BFA561D2B
- generatedChecksum: 2AF2604D6D1923F7C5041044A374E625
  logicalPath: config/default/peripheral/uart
  name: plib_uart_common.h
  physicalPath: peripheral/uart
  security: NON_SECURE
  type: HEADER
  userChecksum: 2AF2604D6D1923F7C5041044A374E625
- generatedChecksum: 285A2ABACB96C59AA5DEB8C8C3B8E876
  logicalPath: packs/ATSAMV71N21B_DFP/component
  name: pmc.h
  physicalPath: ../../packs/ATSAMV71N21B_DFP/component
  security: NON_SECURE
  type: HEADER
  userChecksum: 285A2ABACB96C59AA5DEB8C8C3B8E876
- generatedChecksum: 0FED2123B7911329370226CE4963F82D
  logicalPath: packs/ATSAMV71N21B_DFP/instance
  name: pmc.h
  physicalPath: ../../packs/ATSAMV71N21B_DFP/instance
  security: NON_SECURE
  type: HEADER
  userChecksum: 0FED2123B7911329370226CE4963F82D
- generatedChecksum: 5A686FF678CBFBB4A1FEB86B66DCEC98
  logicalPath: FreeRTOS/Source/include
  name: portable.h
  physicalPath: ../../third_party/rtos/FreeRTOS/Source/include
  security: NON_SECURE
  type: HEADER
  userChecksum: 5A686FF678CBFBB4A1FEB86B66DCEC98
- generatedChecksum: B16F3C9A1AF9C6C726871E79F424A3F9
  logicalPath: FreeRTOS/Source/portable/GCC/SAM/CM7
  name: portmacro.h
  physicalPath: ../../third_party/rtos/FreeRTOS/Source/portable/GCC/SAM/CM7
  security: NON_SECURE
  type: HEADER
  userChecksum: B16F3C9A1AF9C6C726871E79F424A3F9
- generatedChecksum: 696F66B2428CC530389C53B5FE617CE1
  logicalPath: FreeRTOS/Source/include
  name: projdefs.h
  physicalPath: ../../third_party/rtos/FreeRTOS/Source/include
  security: NON_SECURE
  type: HEADER
  userChecksum: 696F66B2428CC530389C53B5FE617CE1
- generatedChecksum: 930DD0099F3AB739C5CE12C0FB228D7A
  logicalPath: packs/ATSAMV71N21B_DFP/component
  name: pwm.h
  physicalPath: ../../packs/ATSAMV71N21B_DFP/component
  security: NON_SECURE
  type: HEADER
  userChecksum: 930DD0099F3AB739C5CE12C0FB228D7A
- generatedChecksum: F4EFE80854C6011F22D2B218F7129026
  logicalPath: packs/ATSAMV71N21B_DFP/instance
  name: pwm0.h
  physicalPath: ../../packs/ATSAMV71N21B_DFP/instance
  security: NON_SECURE
  type: HEADER
  userChecksum: F4EFE80854C6011F22D2B218F7129026
- generatedChecksum: 46DD3ACEFA637580B974544D14264107
  logicalPath: packs/ATSAMV71N21B_DFP/instance
  name: pwm1.h
  physicalPath: ../../packs/ATSAMV71N21B_DFP/instance
  security: NON_SECURE
  type: HEADER
  userChecksum: 46DD3ACEFA637580B974544D14264107
- generatedChecksum: 72DEED7A2E16BCE9721FBFCE20F3B7B0
  logicalPath: packs/ATSAMV71N21B_DFP/component
  name: qspi.h
  physicalPath: ../../packs/ATSAMV71N21B_DFP/component
  security: NON_SECURE
  type: HEADER
  userChecksum: 72DEED7A2E16BCE9721FBFCE20F3B7B0
- generatedChecksum: C53AC72681597888D5EF49FEB5647CD9
  logicalPath: packs/ATSAMV71N21B_DFP/instance
  name: qspi.h
  physicalPath: ../../packs/ATSAMV71N21B_DFP/instance
  security: NON_SECURE
  type: HEADER
  userChecksum: C53AC72681597888D5EF49FEB5647CD9
- generatedChecksum: 6CB1FF8C27E6755C63D75369D1D7A37A
  logicalPath: FreeRTOS/Source/include
  name: queue.h
  physicalPath: ../../third_party/rtos/FreeRTOS/Source/include
  security: NON_SECURE
  type: HEADER
  userChecksum: 6CB1FF8C27E6755C63D75369D1D7A37A
- generatedChecksum: B140BC6B1FBAC0652E8807FCA76FD6FB
  logicalPath: packs/ATSAMV71N21B_DFP/component
  name: rstc.h
  physicalPath: ../../packs/ATSAMV71N21B_DFP/component
  security: NON_SECURE
  type: HEADER
  userChecksum: B140BC6B1FBAC0652E8807FCA76FD6FB
- generatedChecksum: E88FC2F4846FFEFDB47D71A8220DBBD3
  logicalPath: packs/ATSAMV71N21B_DFP/instance
  name: rstc.h
  physicalPath: ../../packs/ATSAMV71N21B_DFP/instance
  security: NON_SECURE
  type: HEADER
  userChecksum: E88FC2F4846FFEFDB47D71A8220DBBD3
- generatedChecksum: 4C868E55D41440AE66E48F408BCA10EA
  logicalPath: packs/ATSAMV71N21B_DFP/component
  name: rswdt.h
  physicalPath: ../../packs/ATSAMV71N21B_DFP/component
  security: NON_SECURE
  type: HEADER
  userChecksum: 4C868E55D41440AE66E48F408BCA10EA
- generatedChecksum: 905813F9E7CD60D618D353C1EEB7686C
  logicalPath: packs/ATSAMV71N21B_DFP/instance
  name: rswdt.h
  physicalPath: ../../packs/ATSAMV71N21B_DFP/instance
  security: NON_SECURE
  type: HEADER
  userChecksum: 905813F9E7CD60D618D353C1EEB7686C
- generatedChecksum: ACF57FA44A7A7C3EE1AC692C045BA2E8
  logicalPath: packs/ATSAMV71N21B_DFP/component
  name: rtc.h
  physicalPath: ../../packs/ATSAMV71N21B_DFP/component
  security: NON_SECURE
  type: HEADER
  userChecksum: ACF57FA44A7A7C3EE1AC692C045BA2E8
- generatedChecksum: 14C7A2C1FD3F1034C167708F6B46E36C
  logicalPath: packs/ATSAMV71N21B_DFP/instance
  name: rtc.h
  physicalPath: ../../packs/ATSAMV71N21B_DFP/instance
  security: NON_SECURE
  type: HEADER
  userChecksum: 14C7A2C1FD3F1034C167708F6B46E36C
- generatedChecksum: 9F0892CA75D9F76679DA8DF02CF2E3B8
  logicalPath: packs/ATSAMV71N21B_DFP/component
  name: rtt.h
  physicalPath: ../../packs/ATSAMV71N21B_DFP/component
  security: NON_SECURE
  type: HEADER
  userChecksum: 9F0892CA75D9F76679DA8DF02CF2E3B8
- generatedChecksum: 1901ADB0E98D48130213C761F50FB6BE
  logicalPath: packs/ATSAMV71N21B_DFP/instance
  name: rtt.h
  physicalPath: ../../packs/ATSAMV71N21B_DFP/instance
  security: NON_SECURE
  type: HEADER
  userChecksum: 1901ADB0E98D48130213C761F50FB6BE
- generatedChecksum: 1E8533A69A99F7D8B5E71A6D2836C487
  logicalPath: packs/ATSAMV71N21B_DFP
  name: samv71n21b.h
  physicalPath: ../../packs/ATSAMV71N21B_DFP
  security: NON_SECURE
  type: HEADER
  userChecksum: 1E8533A69A99F7D8B5E71A6D2836C487
- generatedChecksum: 33DA510D70780FD4E8593233A27CCB78
  logicalPath: packs/ATSAMV71N21B_DFP/pio
  name: samv71n21b.h
  physicalPath: ../../packs/ATSAMV71N21B_DFP/pio
  security: NON_SECURE
  type: HEADER
  userChecksum: 33DA510D70780FD4E8593233A27CCB78
- generatedChecksum: CF169F87C4FC9055695931D40D03251E
  logicalPath: packs/ATSAMV71N21B_DFP/component
  name: sdramc.h
  physicalPath: ../../packs/ATSAMV71N21B_DFP/component
  security: NON_SECURE
  type: HEADER
  userChecksum: CF169F87C4FC9055695931D40D03251E
- generatedChecksum: EFD4919C4F00C449282C5AC64C48A12C
  logicalPath: packs/ATSAMV71N21B_DFP/instance
  name: sdramc.h
  physicalPath: ../../packs/ATSAMV71N21B_DFP/instance
  security: NON_SECURE
  type: HEADER
  userChecksum: EFD4919C4F00C449282C5AC64C48A12C
- generatedChecksum: 9F1AE7D29D09ED8CC21F3DA08049FB79
  logicalPath: FreeRTOS/Source/include
  name: semphr.h
  physicalPath: ../../third_party/rtos/FreeRTOS/Source/include
  security: NON_SECURE
  type: HEADER
  userChecksum: 9F1AE7D29D09ED8CC21F3DA08049FB79
- generatedChecksum: B89CBA1ADC8AB657E0F79BE75F33B419
  logicalPath: packs/ATSAMV71N21B_DFP/component
  name: smc.h
  physicalPath: ../../packs/ATSAMV71N21B_DFP/component
  security: NON_SECURE
  type: HEADER
  userChecksum: B89CBA1ADC8AB657E0F79BE75F33B419
- generatedChecksum: D955B5FE6F0E47F14E71AB5EFB1728DD
  logicalPath: packs/ATSAMV71N21B_DFP/instance
  name: smc.h
  physicalPath: ../../packs/ATSAMV71N21B_DFP/instance
  security: NON_SECURE
  type: HEADER
  userChecksum: D955B5FE6F0E47F14E71AB5EFB1728DD
- generatedChecksum: 269BB14796F5F4F94F123DA65CEED8B3
  logicalPath: packs/ATSAMV71N21B_DFP/component
  name: spi.h
  physicalPath: ../../packs/ATSAMV71N21B_DFP/component
  security: NON_SECURE
  type: HEADER
  userChecksum: 269BB14796F5F4F94F123DA65CEED8B3
- generatedChecksum: DDAAC13A7028C9D9727FBDD7E4571032
  logicalPath: packs/ATSAMV71N21B_DFP/instance
  name: spi0.h
  physicalPath: ../../packs/ATSAMV71N21B_DFP/instance
  security: NON_SECURE
  type: HEADER
  userChecksum: DDAAC13A7028C9D9727FBDD7E4571032
- generatedChecksum: 89C3C2826C463898267A55F7F7C083A5
  logicalPath: packs/ATSAMV71N21B_DFP/instance
  name: spi1.h
  physicalPath: ../../packs/ATSAMV71N21B_DFP/instance
  security: NON_SECURE
  type: HEADER
  userChecksum: 89C3C2826C463898267A55F7F7C083A5
- generatedChecksum: D6EF33F7E7287AB09F21599E664133EE
  logicalPath: packs/ATSAMV71N21B_DFP/component
  name: ssc.h
  physicalPath: ../../packs/ATSAMV71N21B_DFP/component
  security: NON_SECURE
  type: HEADER
  userChecksum: D6EF33F7E7287AB09F21599E664133EE
- generatedChecksum: 0DBEDC214B3697F30520FAB289AC3BF7
  logicalPath: packs/ATSAMV71N21B_DFP/instance
  name: ssc.h
  physicalPath: ../../packs/ATSAMV71N21B_DFP/instance
  security: NON_SECURE
  type: HEADER
  userChecksum: 0DBEDC214B3697F30520FAB289AC3BF7
- generatedChecksum: D0D11C3D2D1BD585018AE271E1AC3B8F
  logicalPath: FreeRTOS/Source/include
  name: stack_macros.h
  physicalPath: ../../third_party/rtos/FreeRTOS/Source/include
  security: NON_SECURE
  type: HEADER
  userChecksum: D0D11C3D2D1BD585018AE271E1AC3B8F
- generatedChecksum: 7C71A9D2BEF16AC21C17ED5C2452C263
  logicalPath: FreeRTOS/Source/include
  name: stream_buffer.h
  physicalPath: ../../third_party/rtos/FreeRTOS/Source/include
  security: NON_SECURE
  type: HEADER
  userChecksum: 7C71A9D2BEF16AC21C17ED5C2452C263
- generatedChecksum: A8ED1F2482E399D17FE0B33C8EB1E864
  logicalPath: packs/ATSAMV71N21B_DFP/component
  name: supc.h
  physicalPath: ../../packs/ATSAMV71N21B_DFP/component
  security: NON_SECURE
  type: HEADER
  userChecksum: A8ED1F2482E399D17FE0B33C8EB1E864
- generatedChecksum: 79F0E1692B21D1A28458F578ABD0284E
  logicalPath: packs/ATSAMV71N21B_DFP/instance
  name: supc.h
  physicalPath: ../../packs/ATSAMV71N21B_DFP/instance
  security: NON_SECURE
  type: HEADER
  userChecksum: 79F0E1692B21D1A28458F578ABD0284E
- generatedChecksum: AFAAF7D896D57569CA4CF73BB3339481
  logicalPath: config/default/system/cache
  name: sys_cache.h
  physicalPath: system/cache
  security: NON_SECURE
  type: HEADER
  userChecksum: AFAAF7D896D57569CA4CF73BB3339481
- generatedChecksum: 6BB6C54C5CD963A5A940CF7BB28F4E10
  logicalPath: config/default/system/debug
  name: sys_debug.h
  physicalPath: system/debug
  security: NON_SECURE
  type: HEADER
  userChecksum: 6BB6C54C5CD963A5A940CF7BB28F4E10
- generatedChecksum: 1329D2DEB6E5AC9515AD4D165C60DC74
  logicalPath: config/default/system/int
  name: sys_int.h
  physicalPath: system/int
  security: NON_SECURE
  type: HEADER
  userChecksum: 1329D2DEB6E5AC9515AD4D165C60DC74
- generatedChecksum: 00278F169FFB0CBBAB3A68B5D647F093
  logicalPath: config/default/system/int
  name: sys_int_mapping.h
  physicalPath: system/int
  security: NON_SECURE
  type: HEADER
  userChecksum: 00278F169FFB0CBBAB3A68B5D647F093
- generatedChecksum: 466D676839280C0E7FC2CC6F78BA6EE9
  logicalPath: config/default/system/time
  name: sys_time.h
  physicalPath: system/time
  security: NON_SECURE
  type: HEADER
  userChecksum: 466D676839280C0E7FC2CC6F78BA6EE9
- generatedChecksum: 125CB4EFA4E80BCD6041E8AC22F2E2FC
  logicalPath: config/default/system/time
  name: sys_time_definitions.h
  physicalPath: system/time
  security: NON_SECURE
  type: HEADER
  userChecksum: 125CB4EFA4E80BCD6041E8AC22F2E2FC
- generatedChecksum: 62F39464265EC34979649F761FB4FE57
  logicalPath: config/default/system/time
  name: sys_time_local.h
  physicalPath: system/time/src
  security: NON_SECURE
  type: HEADER
  userChecksum: 62F39464265EC34979649F761FB4FE57
- generatedChecksum: BE95B4F134C5C929787B9DA6FDBF3501
  logicalPath: config/default/system
  name: system.h
  physicalPath: system
  security: NON_SECURE
  type: HEADER
  userChecksum: BE95B4F134C5C929787B9DA6FDBF3501
- generatedChecksum: C3F5136D520DAC4416512EBFCCA023C3
  logicalPath: config/default/system
  name: system_common.h
  physicalPath: system
  security: NON_SECURE
  type: HEADER
  userChecksum: C3F5136D520DAC4416512EBFCCA023C3
- generatedChecksum: 1C75A8A6B60598A2FD0D533F57839B72
  logicalPath: config/default/system
  name: system_module.h
  physicalPath: system
  security: NON_SECURE
  type: HEADER
  userChecksum: 1C75A8A6B60598A2FD0D533F57839B72
- generatedChecksum: 84B3224817BDD8B37961BB3B3441E134
  logicalPath: FreeRTOS/Source/include
  name: task.h
  physicalPath: ../../third_party/rtos/FreeRTOS/Source/include
  security: NON_SECURE
  type: HEADER
  userChecksum: 84B3224817BDD8B37961BB3B3441E134
- generatedChecksum: E20E40000C2C5AEF32D35EF813A1905E
  logicalPath: packs/ATSAMV71N21B_DFP/component
  name: tc.h
  physicalPath: ../../packs/ATSAMV71N21B_DFP/component
  security: NON_SECURE
  type: HEADER
  userChecksum: E20E40000C2C5AEF32D35EF813A1905E
- generatedChecksum: A20CC602CA8E194135B90F3E47BD439C
  logicalPath: packs/ATSAMV71N21B_DFP/instance
  name: tc0.h
  physicalPath: ../../packs/ATSAMV71N21B_DFP/instance
  security: NON_SECURE
  type: HEADER
  userChecksum: A20CC602CA8E194135B90F3E47BD439C
- generatedChecksum: E8FF72FA5CEC3C65A9626DD5692ADE5F
  logicalPath: packs/ATSAMV71N21B_DFP/instance
  name: tc1.h
  physicalPath: ../../packs/ATSAMV71N21B_DFP/instance
  security: NON_SECURE
  type: HEADER
  userChecksum: E8FF72FA5CEC3C65A9626DD5692ADE5F
- generatedChecksum: 66795BDA4AF9E86E48A604708C906933
  logicalPath: packs/ATSAMV71N21B_DFP/instance
  name: tc2.h
  physicalPath: ../../packs/ATSAMV71N21B_DFP/instance
  security: NON_SECURE
  type: HEADER
  userChecksum: 66795BDA4AF9E86E48A604708C906933
- generatedChecksum: 3160A0FBF453DE685FD22FD7EACD1226
  logicalPath: packs/ATSAMV71N21B_DFP/instance
  name: tc3.h
  physicalPath: ../../packs/ATSAMV71N21B_DFP/instance
  security: NON_SECURE
  type: HEADER
  userChecksum: 3160A0FBF453DE685FD22FD7EACD1226
- generatedChecksum: C8BB70E2423A57902E9FDC0C9EC81F8D
  logicalPath: FreeRTOS/Source/include
  name: timers.h
  physicalPath: ../../third_party/rtos/FreeRTOS/Source/include
  security: NON_SECURE
  type: HEADER
  userChecksum: C8BB70E2423A57902E9FDC0C9EC81F8D
- generatedChecksum: E7B1CC92ABE4830B5244251AB8FA4FB0
  logicalPath: config/default
  name: toolchain_specifics.h
  physicalPath: ''
  security: NON_SECURE
  type: HEADER
  userChecksum: E7B1CC92ABE4830B5244251AB8FA4FB0
- generatedChecksum: A9C05662C9D28F4A5F6D6EA56CA4755E
  logicalPath: packs/ATSAMV71N21B_DFP/component
  name: trng.h
  physicalPath: ../../packs/ATSAMV71N21B_DFP/component
  security: NON_SECURE
  type: HEADER
  userChecksum: A9C05662C9D28F4A5F6D6EA56CA4755E
- generatedChecksum: 87287CE0304F9B65650813BA05731C79
  logicalPath: packs/ATSAMV71N21B_DFP/instance
  name: trng.h
  physicalPath: ../../packs/ATSAMV71N21B_DFP/instance
  security: NON_SECURE
  type: HEADER
  userChecksum: 87287CE0304F9B65650813BA05731C79
- generatedChecksum: 17504AE8631098B362CA669A0C66E364
  logicalPath: packs/ATSAMV71N21B_DFP/component
  name: twihs.h
  physicalPath: ../../packs/ATSAMV71N21B_DFP/component
  security: NON_SECURE
  type: HEADER
  userChecksum: 17504AE8631098B362CA669A0C66E364
- generatedChecksum: 3BBEA8FA20E417297AEAB84B71380D8B
  logicalPath: packs/ATSAMV71N21B_DFP/instance
  name: twihs0.h
  physicalPath: ../../packs/ATSAMV71N21B_DFP/instance
  security: NON_SECURE
  type: HEADER
  userChecksum: 3BBEA8FA20E417297AEAB84B71380D8B
- generatedChecksum: 9A89397AA88C33794E5603AF11BEB3E5
  logicalPath: packs/ATSAMV71N21B_DFP/instance
  name: twihs1.h
  physicalPath: ../../packs/ATSAMV71N21B_DFP/instance
  security: NON_SECURE
  type: HEADER
  userChecksum: 9A89397AA88C33794E5603AF11BEB3E5
- generatedChecksum: 76113E34C5AADBFEA9E200350DF927BB
  logicalPath: packs/ATSAMV71N21B_DFP/instance
  name: twihs2.h
  physicalPath: ../../packs/ATSAMV71N21B_DFP/instance
  security: NON_SECURE
  type: HEADER
  userChecksum: 76113E34C5AADBFEA9E200350DF927BB
- generatedChecksum: 5A48CB318846B049B9FB19940672ABB9
  logicalPath: packs/ATSAMV71N21B_DFP/component
  name: uart.h
  physicalPath: ../../packs/ATSAMV71N21B_DFP/component
  security: NON_SECURE
  type: HEADER
  userChecksum: 5A48CB318846B049B9FB19940672ABB9
- generatedChecksum: EA53F830FFFAF6A101C8EB0957FEBCB4
  logicalPath: packs/ATSAMV71N21B_DFP/instance
  name: uart0.h
  physicalPath: ../../packs/ATSAMV71N21B_DFP/instance
  security: NON_SECURE
  type: HEADER
  userChecksum: EA53F830FFFAF6A101C8EB0957FEBCB4
- generatedChecksum: C45430668C134EC82E175E52D714A755
  logicalPath: packs/ATSAMV71N21B_DFP/instance
  name: uart1.h
  physicalPath: ../../packs/ATSAMV71N21B_DFP/instance
  security: NON_SECURE
  type: HEADER
  userChecksum: C45430668C134EC82E175E52D714A755
- generatedChecksum: DBF89FD4966738115F54F4A1C5DB77C3
  logicalPath: packs/ATSAMV71N21B_DFP/instance
  name: uart2.h
  physicalPath: ../../packs/ATSAMV71N21B_DFP/instance
  security: NON_SECURE
  type: HEADER
  userChecksum: DBF89FD4966738115F54F4A1C5DB77C3
- generatedChecksum: BE491CF71BF8726A80E04ADCAD2BBBAF
  logicalPath: packs/ATSAMV71N21B_DFP/instance
  name: uart3.h
  physicalPath: ../../packs/ATSAMV71N21B_DFP/instance
  security: NON_SECURE
  type: HEADER
  userChecksum: BE491CF71BF8726A80E04ADCAD2BBBAF
- generatedChecksum: E3B4FAB09D805DC2A769DBF85F21A150
  logicalPath: packs/ATSAMV71N21B_DFP/instance
  name: uart4.h
  physicalPath: ../../packs/ATSAMV71N21B_DFP/instance
  security: NON_SECURE
  type: HEADER
  userChecksum: E3B4FAB09D805DC2A769DBF85F21A150
- generatedChecksum: CB29D346F0587626A7D56A7EEC76E68D
  logicalPath: packs/ATSAMV71N21B_DFP/component
  name: usart.h
  physicalPath: ../../packs/ATSAMV71N21B_DFP/component
  security: NON_SECURE
  type: HEADER
  userChecksum: CB29D346F0587626A7D56A7EEC76E68D
- generatedChecksum: 41BE81E215044465249F24C550C24759
  logicalPath: packs/ATSAMV71N21B_DFP/instance
  name: usart0.h
  physicalPath: ../../packs/ATSAMV71N21B_DFP/instance
  security: NON_SECURE
  type: HEADER
  userChecksum: 41BE81E215044465249F24C550C24759
- generatedChecksum: F5ABA3DD68904192B52A9B85F48744C0
  logicalPath: packs/ATSAMV71N21B_DFP/instance
  name: usart1.h
  physicalPath: ../../packs/ATSAMV71N21B_DFP/instance
  security: NON_SECURE
  type: HEADER
  userChecksum: F5ABA3DD68904192B52A9B85F48744C0
- generatedChecksum: 8DF0738852521E027D9CCE3B9BB94F18
  logicalPath: packs/ATSAMV71N21B_DFP/instance
  name: usart2.h
  physicalPath: ../../packs/ATSAMV71N21B_DFP/instance
  security: NON_SECURE
  type: HEADER
  userChecksum: 8DF0738852521E027D9CCE3B9BB94F18
- generatedChecksum: 39659CDE2CC726544BD68544FB7EF4B2
  logicalPath: config/default/usb
  name: usb_chapter_9.h
  physicalPath: usb
  security: NON_SECURE
  type: HEADER
  userChecksum: 39659CDE2CC726544BD68544FB7EF4B2
- generatedChecksum: E7B6EAD8687A8EBC0355E0CE413B6A87
  logicalPath: config/default/usb
  name: usb_common.h
  physicalPath: usb
  security: NON_SECURE
  type: HEADER
  userChecksum: E7B6EAD8687A8EBC0355E0CE413B6A87
- generatedChecksum: 68F7DBD311EDCAF1098CDF2FD15B8C73
  logicalPath: config/default/usb
  name: usb_device.h
  physicalPath: usb
  security: NON_SECURE
  type: HEADER
  userChecksum: 68F7DBD311EDCAF1098CDF2FD15B8C73
- generatedChecksum: 626BFDDD140B808E90C9DD2E4A27421E
  logicalPath: config/default/usb/src
  name: usb_device_function_driver.h
  physicalPath: usb/src
  security: NON_SECURE
  type: HEADER
  userChecksum: 626BFDDD140B808E90C9DD2E4A27421E
- generatedChecksum: 144BD1138A70A9AA387E3742DB6E7448
  logicalPath: config/default/usb
  name: usb_device_hid.h
  physicalPath: usb
  security: NON_SECURE
  type: HEADER
  userChecksum: 144BD1138A70A9AA387E3742DB6E7448
- generatedChecksum: 6C72D678DC0100860FD1086BCF4A22C5
  logicalPath: config/default/usb/src
  name: usb_device_hid_local.h
  physicalPath: usb/src
  security: NON_SECURE
  type: HEADER
  userChecksum: 6C72D678DC0100860FD1086BCF4A22C5
- generatedChecksum: 9B727D396CAEBD5FCB12F1F8264C4FD9
  logicalPath: config/default/usb/src
  name: usb_device_local.h
  physicalPath: usb/src
  security: NON_SECURE
  type: HEADER
  userChecksum: 9B727D396CAEBD5FCB12F1F8264C4FD9
- generatedChecksum: C8D4A1D9092FD842506F565CE9B8C265
  logicalPath: config/default/usb/src
  name: usb_device_mapping.h
  physicalPath: usb/src
  security: NON_SECURE
  type: HEADER
  userChecksum: C8D4A1D9092FD842506F565CE9B8C265
- generatedChecksum: 6C4A6859DB16EA8C046F995C6B6C1C6F
  logicalPath: config/default/usb/src
  name: usb_external_dependencies.h
  physicalPath: usb/src
  security: NON_SECURE
  type: HEADER
  userChecksum: 6C4A6859DB16EA8C046F995C6B6C1C6F
- generatedChecksum: F258661D72F9E844BF936D43BF859BE7
  logicalPath: config/default/usb
  name: usb_hid.h
  physicalPath: usb
  security: NON_SECURE
  type: HEADER
  userChecksum: F258661D72F9E844BF936D43BF859BE7
- generatedChecksum: F127C67A3E33E5788C0F057F648EE57C
  logicalPath: config/default/usb
  name: usb_host.h
  physicalPath: usb
  security: NON_SECURE
  type: HEADER
  userChecksum: F127C67A3E33E5788C0F057F648EE57C
- generatedChecksum: 6EBC5E4D06FC96A02ADF3B7416957DD6
  logicalPath: config/default/usb
  name: usb_host_client_driver.h
  physicalPath: usb
  security: NON_SECURE
  type: HEADER
  userChecksum: 6EBC5E4D06FC96A02ADF3B7416957DD6
- generatedChecksum: 757C8484C955543C893361992D11FD4C
  logicalPath: config/default/usb
  name: usb_host_hub_interface.h
  physicalPath: usb
  security: NON_SECURE
  type: HEADER
  userChecksum: 757C8484C955543C893361992D11FD4C
- generatedChecksum: 3E3CC6BC9128194CB4D19F29C57E312B
  logicalPath: config/default/usb
  name: usb_hub.h
  physicalPath: usb
  security: NON_SECURE
  type: HEADER
  userChecksum: 3E3CC6BC9128194CB4D19F29C57E312B
- generatedChecksum: 8DB286A8248F5F1AA40DE6A11B38D847
  logicalPath: packs/ATSAMV71N21B_DFP/component
  name: usbhs.h
  physicalPath: ../../packs/ATSAMV71N21B_DFP/component
  security: NON_SECURE
  type: HEADER
  userChecksum: 8DB286A8248F5F1AA40DE6A11B38D847
- generatedChecksum: AB10AA1EF03FCD2400DD1D1BB25B875B
  logicalPath: packs/ATSAMV71N21B_DFP/instance
  name: usbhs.h
  physicalPath: ../../packs/ATSAMV71N21B_DFP/instance
  security: NON_SECURE
  type: HEADER
  userChecksum: AB10AA1EF03FCD2400DD1D1BB25B875B
- generatedChecksum: null
  logicalPath: config/default
  name: user.h
  physicalPath: ''
  security: NON_SECURE
  type: HEADER
  userChecksum: null
- generatedChecksum: AC9615149E87C74317CD8C3C553D295A
  logicalPath: packs/ATSAMV71N21B_DFP/component
  name: utmi.h
  physicalPath: ../../packs/ATSAMV71N21B_DFP/component
  security: NON_SECURE
  type: HEADER
  userChecksum: AC9615149E87C74317CD8C3C553D295A
- generatedChecksum: B73F5251DEE493B7A02E1C55C3EF090B
  logicalPath: packs/ATSAMV71N21B_DFP/instance
  name: utmi.h
  physicalPath: ../../packs/ATSAMV71N21B_DFP/instance
  security: NON_SECURE
  type: HEADER
  userChecksum: B73F5251DEE493B7A02E1C55C3EF090B
- generatedChecksum: 6F5164EAC3A583717F29658106C20539
  logicalPath: packs/ATSAMV71N21B_DFP/component
  name: wdt.h
  physicalPath: ../../packs/ATSAMV71N21B_DFP/component
  security: NON_SECURE
  type: HEADER
  userChecksum: 6F5164EAC3A583717F29658106C20539
- generatedChecksum: 205D318B1CF4589CCF184BE1DEEDF338
  logicalPath: packs/ATSAMV71N21B_DFP/instance
  name: wdt.h
  physicalPath: ../../packs/ATSAMV71N21B_DFP/instance
  security: NON_SECURE
  type: HEADER
  userChecksum: 205D318B1CF4589CCF184BE1DEEDF338
- generatedChecksum: 9CDA513B79A95DBC94CD8DC0C3D37F45
  logicalPath: packs/ATSAMV71N21B_DFP/component
  name: xdmac.h
  physicalPath: ../../packs/ATSAMV71N21B_DFP/component
  security: NON_SECURE
  type: HEADER
  userChecksum: 9CDA513B79A95DBC94CD8DC0C3D37F45
- generatedChecksum: 92B7ABF4E692F389CA02397077B3808D
  logicalPath: packs/ATSAMV71N21B_DFP/instance
  name: xdmac.h
  physicalPath: ../../packs/ATSAMV71N21B_DFP/instance
  security: NON_SECURE
  type: HEADER
  userChecksum: 92B7ABF4E692F389CA02397077B3808D
- generatedChecksum: 7BAAE2044DF2073B395A4A0003B222A8
  logicalPath: config/default
  name: ATSAMV71N21B.ld
  physicalPath: ''
  security: NON_SECURE
  type: LINKER
  userChecksum: 7BAAE2044DF2073B395A4A0003B222A8
format_version: v1.0
libraries: []
settings:
- append: true
  category: C32
  delimiter: ;
  key: extra-include-directories
  security: NON_SECURE
  value: ../src/third_party/rtos/FreeRTOS/Source/include;
- append: true
  category: C32
  delimiter: ;
  key: extra-include-directories
  security: NON_SECURE
  value: ../src/third_party/rtos/FreeRTOS/Source/portable/GCC/SAM/CM7;
- append: true
  category: C32
  delimiter: ;
  key: extra-include-directories
  security: NON_SECURE
  value: ../src;../src/config/default;../src/packs/ATSAMV71N21B_DFP;../src/packs/CMSIS/CMSIS/Core/Include;../src/packs/CMSIS/
- append: false
  category: C32-LD
  delimiter: ''
  key: heap-size
  security: NON_SECURE
  value: '512'
- append: false
  category: C32-LD
  delimiter: ''
  key: no-device-startup-code
  security: NON_SECURE
  value: 'true'
- append: true
  category: C32-LD
  delimiter: ;=
  key: preprocessor-macros
  security: NON_SECURE
  value: ''
- append: true
  category: C32CPP
  delimiter: ;
  key: extra-include-directories
  security: NON_SECURE
  value: ../src/third_party/rtos/FreeRTOS/Source/include;../src/third_party/rtos/FreeRTOS/Source/portable/GCC/SAM/CM7;
- append: true
  category: C32CPP
  delimiter: ;
  key: extra-include-directories
  security: NON_SECURE
  value: ../src;../src/config/default;../src/packs/ATSAMV71N21B_DFP;../src/packs/CMSIS/CMSIS/Core/Include;../src/packs/CMSIS/
- append: false
  category: C32Global
  delimiter: ''
  key: mdtcm
  security: NON_SECURE
  value: ''
- append: false
  category: C32Global
  delimiter: ''
  key: mitcm
  security: NON_SECURE
  value: ''
- append: false
  category: C32Global
  delimiter: ''
  key: mstacktcm
  security: NON_SECURE
  value: 'false'
sourcePaths: []
