bemcgarvey/SAMduino/firmware/FullDemo/firmware/src/config/default/configuration.h

/*******************************************************************************
  System Configuration Header

  File Name:
    configuration.h

  Summary:
    Build-time configuration header for the system defined by this project.

  Description:
    An MPLAB Project may have multiple configurations.  This file defines the
    build-time options for a single configuration.

  Remarks:
    This configuration header must not define any prototypes or data
    definitions (or include any files that do).  It only provides macro
    definitions for build-time configuration options

*******************************************************************************/

// DOM-IGNORE-BEGIN
/*******************************************************************************
* Copyright (C) 2018 Microchip Technology Inc. and its subsidiaries.
*
* Subject to your compliance with these terms, you may use Microchip software
* and any derivatives exclusively with Microchip products. It is your
* responsibility to comply with third party license terms applicable to your
* use of third party software (including open source software) that may
* accompany Microchip software.
*
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
* IN NO EVENT WILL MICROCHIP BE LIABLE FOR ANY INDIRECT, SPECIAL, PUNITIVE,
* INCIDENTAL OR CONSEQUENTIAL LOSS, DAMAGE, COST OR EXPENSE OF ANY KIND
* WHATSOEVER RELATED TO THE SOFTWARE, HOWEVER CAUSED, EVEN IF MICROCHIP HAS
* BEEN ADVISED OF THE POSSIBILITY OR THE DAMAGES ARE FORESEEABLE. TO THE
* FULLEST EXTENT ALLOWED BY LAW, MICROCHIP'S TOTAL LIABILITY ON ALL CLAIMS IN
* ANY WAY RELATED TO THIS SOFTWARE WILL NOT EXCEED THE AMOUNT OF FEES, IF ANY,
* THAT YOU HAVE PAID DIRECTLY TO MICROCHIP FOR THIS SOFTWARE.
*******************************************************************************/
// DOM-IGNORE-END

#ifndef CONFIGURATION_H
#define CONFIGURATION_H

// *****************************************************************************
// *****************************************************************************
// Section: Included Files
// *****************************************************************************
// *****************************************************************************
/*  This section Includes other configuration headers necessary to completely
    define this configuration.
*/

#include "user.h"
#include "device.h"

// DOM-IGNORE-BEGIN
#ifdef __cplusplus  // Provide C++ Compatibility

extern "C" {

#endif
// DOM-IGNORE-END

// *****************************************************************************
// *****************************************************************************
// Section: System Configuration
// *****************************************************************************
// *****************************************************************************



// *****************************************************************************
// *****************************************************************************
// Section: System Service Configuration
// *****************************************************************************
// *****************************************************************************
/* TIME System Service Configuration Options */
#define SYS_TIME_INDEX_0                            (0)
#define SYS_TIME_MAX_TIMERS                         (5)
#define SYS_TIME_HW_COUNTER_WIDTH                   (16)
#define SYS_TIME_HW_COUNTER_PERIOD                  (65535U)
#define SYS_TIME_HW_COUNTER_HALF_PERIOD             (SYS_TIME_HW_COUNTER_PERIOD>>1)
#define SYS_TIME_CPU_CLOCK_FREQUENCY                (300000000)
#define SYS_TIME_COMPARE_UPDATE_EXECUTION_CYCLES    (900)



// *****************************************************************************
// *****************************************************************************
// Section: Driver Configuration
// *****************************************************************************
// *****************************************************************************
/* SST26 Driver Instance Configuration */
#define DRV_SST26_INDEX                 0
#define DRV_SST26_CLIENTS_NUMBER        1
#define DRV_SST26_START_ADDRESS         0x0
#define DRV_SST26_PAGE_SIZE             256
#define DRV_SST26_ERASE_BUFFER_SIZE     4096



// *****************************************************************************
// *****************************************************************************
// Section: Middleware & Other Library Configuration
// *****************************************************************************
// *****************************************************************************
/* Number of Endpoints used */
#define DRV_USBHSV1_ENDPOINTS_NUMBER                        3

/* The USB Device Layer will not initialize the USB Driver */
#define USB_DEVICE_DRIVER_INITIALIZE_EXPLICIT

/* Maximum device layer instances */
#define USB_DEVICE_INSTANCES_NUMBER                         1

/* EP0 size in bytes */
#define USB_DEVICE_EP0_BUFFER_SIZE                          64

/* Enable SOF Events */
#define USB_DEVICE_SOF_EVENT_ENABLE





/*** USB Driver Configuration ***/

/* Maximum USB driver instances */
#define DRV_USBHSV1_INSTANCES_NUMBER                        1

/* Interrupt mode enabled */
#define DRV_USBHSV1_INTERRUPT_MODE                          true

/* Enables Device Support */
#define DRV_USBHSV1_DEVICE_SUPPORT                          true
	
/* Disable Host Support */
#define DRV_USBHSV1_HOST_SUPPORT                            false

/* Alignment for buffers that are submitted to USB Driver*/ 
#define USB_ALIGN  CACHE_ALIGN

/* Maximum instances of HID function driver */
#define USB_DEVICE_HID_INSTANCES_NUMBER     1 

/* HID Transfer Queue Size for both read and
   write. Applicable to all instances of the
   function driver */
#define USB_DEVICE_HID_QUEUE_DEPTH_COMBINED                 2



// *****************************************************************************
// *****************************************************************************
// Section: Application Configuration
// *****************************************************************************
// *****************************************************************************


//DOM-IGNORE-BEGIN
#ifdef __cplusplus
}
#endif
//DOM-IGNORE-END

#endif // CONFIGURATION_H
/*******************************************************************************
 End of File
*/
