bemcgarvey/SAMduino/firmware/FullDemo/firmware/src/config/default/peripheral/pwm/plib_pwm0.c

/*******************************************************************************
  PWM Peripheral Library Interface Source File

  Company
    Microchip Technology Inc.

  File Name
    plib_PWM0.c

  Summary
    PWM0 peripheral library source file.

  Description
    This file implements the interface to the PWM peripheral library.  This
    library provides access to and control of the associated peripheral
    instance.

*******************************************************************************/

// DOM-IGNORE-BEGIN
/*******************************************************************************
* Copyright (C) 2018 Microchip Technology Inc. and its subsidiaries.
*
* Subject to your compliance with these terms, you may use Microchip software
* and any derivatives exclusively with Microchip products. It is your
* responsibility to comply with third party license terms applicable to your
* use of third party software (including open source software) that may
* accompany Microchip software.
*
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
* IN NO EVENT WILL MICROCHIP BE LIABLE FOR ANY INDIRECT, SPECIAL, PUNITIVE,
* INCIDENTAL OR CONSEQUENTIAL LOSS, DAMAGE, COST OR EXPENSE OF ANY KIND
* WHATSOEVER RELATED TO THE SOFTWARE, HOWEVER CAUSED, EVEN IF MICROCHIP HAS
* BEEN ADVISED OF THE POSSIBILITY OR THE DAMAGES ARE FORESEEABLE. TO THE
* FULLEST EXTENT ALLOWED BY LAW, MICROCHIP'S TOTAL LIABILITY ON ALL CLAIMS IN
* ANY WAY RELATED TO THIS SOFTWARE WILL NOT EXCEED THE AMOUNT OF FEES, IF ANY,
* THAT YOU HAVE PAID DIRECTLY TO MICROCHIP FOR THIS SOFTWARE.
*******************************************************************************/
// DOM-IGNORE-END


// *****************************************************************************
// *****************************************************************************
// Section: Included Files
// *****************************************************************************
// *****************************************************************************

/*  This section lists the other files that are included in this file.
*/
#include "device.h"
#include "plib_pwm0.h"
#include "interrupts.h"



/* Initialize enabled PWM channels */
void PWM0_Initialize (void)
{
    /* Clock configuration */
    PWM0_REGS->PWM_CLK = PWM_CLK_PREA_CLK_DIV2 | PWM_CLK_DIVA(75);

    /************** Channel 0 *************************/
    /* PWM channel mode configurations */
    PWM0_REGS->PWM_CH_NUM[0].PWM_CMR = PWM_CMR_CPRE_CLKA | PWM_CMR_CALG_LEFT_ALIGNED
                    | PWM_CMR_CPOL_LOW_POLARITY ;

    /* PWM period */
    PWM0_REGS->PWM_CH_NUM[0].PWM_CPRD = 20000U;

    /* PWM duty cycle */
    PWM0_REGS->PWM_CH_NUM[0].PWM_CDTY = 500U;
 
     

    /************** Channel 1 *************************/
    /* PWM channel mode configurations */
    PWM0_REGS->PWM_CH_NUM[1].PWM_CMR = PWM_CMR_CPRE_MCK | PWM_CMR_CALG_LEFT_ALIGNED
                    | PWM_CMR_CPOL_LOW_POLARITY | (PWM_CMR_DTE_Msk);

    /* PWM period */
    PWM0_REGS->PWM_CH_NUM[1].PWM_CPRD = 7500U;

    /* PWM duty cycle */
    PWM0_REGS->PWM_CH_NUM[1].PWM_CDTY = 0U;
    /* Dead time */
    PWM0_REGS->PWM_CH_NUM[1].PWM_DT = (150U << PWM_DT_DTL_Pos) | (150U);
         
     
 
 
}

/* Start the PWM generation */
void PWM0_ChannelsStart (PWM_CHANNEL_MASK channelMask)
{
    PWM0_REGS->PWM_ENA = channelMask;
}

/* Stop the PWM generation */
void PWM0_ChannelsStop (PWM_CHANNEL_MASK channelMask)
{
    PWM0_REGS->PWM_DIS = channelMask;
}

/* configure PWM period */
void PWM0_ChannelPeriodSet (PWM_CHANNEL_NUM channel, uint16_t period)
{
    PWM0_REGS->PWM_CH_NUM[channel].PWM_CPRDUPD = period;
}

/* Read PWM period */
uint16_t PWM0_ChannelPeriodGet (PWM_CHANNEL_NUM channel)
{
    return (uint16_t)PWM0_REGS->PWM_CH_NUM[channel].PWM_CPRD;
}

/* Configure dead time */
void PWM0_ChannelDeadTimeSet (PWM_CHANNEL_NUM channel, uint16_t deadtime_high, uint16_t deadtime_low)
{
    PWM0_REGS->PWM_CH_NUM[channel].PWM_DTUPD = ((deadtime_low << PWM_DT_DTL_Pos) | deadtime_high);
}

/* Configure compare unit value */
void PWM0_CompareValueSet (PWM_COMPARE cmp_unit, uint16_t cmp_value)
{
    PWM0_REGS->PWM_CMP[cmp_unit].PWM_CMPVUPD = cmp_value;
}

/* Enable counter event */
void PWM0_ChannelCounterEventEnable (PWM_CHANNEL_MASK channelMask)
{
    PWM0_REGS->PWM_IER1 = channelMask;
}

/* Disable counter event */
void PWM0_ChannelCounterEventDisable (PWM_CHANNEL_MASK channelMask)
{
    PWM0_REGS->PWM_IDR1 = channelMask;
}


/* Enable synchronous update */
void PWM0_SyncUpdateEnable (void)
{
    PWM0_REGS->PWM_SCUC = PWM_SCUC_UPDULOCK_Msk;
}

/* Clear the fault status */
void PWM0_FaultStatusClear(PWM_FAULT_ID fault_id)
{
    PWM0_REGS->PWM_FCR = 0x1U << fault_id;
}

/* Override PWM outputs */
void PWM0_ChannelOverrideEnable(PWM_CHANNEL_NUM channel)
{
    PWM0_REGS->PWM_OS &= ~((1 << channel) | (1 << (channel + 16)));
    PWM0_REGS->PWM_OS |= ((0 << channel) | (0 << (channel + 16)));
}

/* Disable override of PWM outputs */
void PWM0_ChannelOverrideDisable(PWM_CHANNEL_NUM channel)
{
    PWM0_REGS->PWM_OS |= ((1 << channel) | (1 << (channel + 16)));
}


/* Check the status of counter event */
bool PWM0_ChannelCounterEventStatusGet (PWM_CHANNEL_NUM channel)
{
    bool status;
    status = (PWM0_REGS->PWM_ISR1 >> channel) & 0x1U;
    return status;
}

/**
 End of File
*/
