bemcgarvey/SAMduino/firmware/FullDemo/firmware/src/config/default/initialization.c

/*******************************************************************************
  System Initialization File

  File Name:
    initialization.c

  Summary:
    This file contains source code necessary to initialize the system.

  Description:
    This file contains source code necessary to initialize the system.  It
    implements the "SYS_Initialize" function, defines the configuration bits,
    and allocates any necessary global system resources,
 *******************************************************************************/

// DOM-IGNORE-BEGIN
/*******************************************************************************
* Copyright (C) 2018 Microchip Technology Inc. and its subsidiaries.
*
* Subject to your compliance with these terms, you may use Microchip software
* and any derivatives exclusively with Microchip products. It is your
* responsibility to comply with third party license terms applicable to your
* use of third party software (including open source software) that may
* accompany Microchip software.
*
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
* IN NO EVENT WILL MICROCHIP BE LIABLE FOR ANY INDIRECT, SPECIAL, PUNITIVE,
* INCIDENTAL OR CONSEQUENTIAL LOSS, DAMAGE, COST OR EXPENSE OF ANY KIND
* WHATSOEVER RELATED TO THE SOFTWARE, HOWEVER CAUSED, EVEN IF MICROCHIP HAS
* BEEN ADVISED OF THE POSSIBILITY OR THE DAMAGES ARE FORESEEABLE. TO THE
* FULLEST EXTENT ALLOWED BY LAW, MICROCHIP'S TOTAL LIABILITY ON ALL CLAIMS IN
* ANY WAY RELATED TO THIS SOFTWARE WILL NOT EXCEED THE AMOUNT OF FEES, IF ANY,
* THAT YOU HAVE PAID DIRECTLY TO MICROCHIP FOR THIS SOFTWARE.
 *******************************************************************************/
// DOM-IGNORE-END

// *****************************************************************************
// *****************************************************************************
// Section: Included Files
// *****************************************************************************
// *****************************************************************************
#include "configuration.h"
#include "definitions.h"
#include "device.h"



// ****************************************************************************
// ****************************************************************************
// Section: Configuration Bits
// ****************************************************************************
// ****************************************************************************
#pragma config TCM_CONFIGURATION = 0
#pragma config SECURITY_BIT = CLEAR
#pragma config BOOT_MODE = SET




// *****************************************************************************
// *****************************************************************************
// Section: Driver Initialization Data
// *****************************************************************************
// *****************************************************************************
// <editor-fold defaultstate="collapsed" desc="DRV_SST26 Initialization Data">

const DRV_SST26_PLIB_INTERFACE drvSST26PlibAPI = {
    .CommandWrite   = QSPI_CommandWrite,
    .RegisterRead   = QSPI_RegisterRead,
    .RegisterWrite  = QSPI_RegisterWrite,
    .MemoryRead     = QSPI_MemoryRead,
    .MemoryWrite    = QSPI_MemoryWrite
};

const DRV_SST26_INIT drvSST26InitData =
{
    .sst26Plib      = &drvSST26PlibAPI,
};
// </editor-fold>



// *****************************************************************************
// *****************************************************************************
// Section: System Data
// *****************************************************************************
// *****************************************************************************
/* Structure to hold the object handles for the modules in the system. */
SYSTEM_OBJECTS sysObj;

// *****************************************************************************
// *****************************************************************************
// Section: Library/Stack Initialization Data
// *****************************************************************************
// *****************************************************************************
/******************************************************
 * USB Driver Initialization
 ******************************************************/

/*  When designing a Self-powered USB Device, the application should make sure
    that USB_DEVICE_Attach() function is called only when VBUS is actively powered.
	Therefore, the firmware needs some means to detect when the Host is powering 
	the VBUS. A 5V tolerant I/O pin can be connected to VBUS (through a resistor)
	and can be used to detect when VBUS is high or low. The application can specify
	a VBUS Detect function through the USB Driver Initialize data structure. 
	The USB device stack will periodically call this function. If the VBUS is 
	detected, the USB_DEVICE_EVENT_POWER_DETECTED event is generated. If the VBUS 
	is removed (i.e., the device is physically detached from Host), the USB stack 
	will generate the event USB_DEVICE_EVENT_POWER_REMOVED. The application should 
	call USB_DEVICE_Detach() when VBUS is removed. 

    The following are the steps to generate the VBUS_SENSE Function through MHC     
        1) Navigate to MHC->Tools->Pin Configuration and Configure the pin used 
		   as VBUS_SENSE. Set this pin Function as "GPIO" and set as "Input". 
		   Provide a custom name to the pin.
        2) Select the USB Driver Component in MHC Project Graph and enable the  
		   "Enable VBUS Sense" Check-box.     
        3) Specify the custom name of the VBUS SENSE pin in the "VBUS SENSE Pin Name" box.  
*/
	  
	
static DRV_USB_VBUS_LEVEL DRV_USBHSV1_VBUS_Comparator(void)
{
    DRV_USB_VBUS_LEVEL retVal = DRV_USB_VBUS_LEVEL_INVALID;
    if(true == USB_VBUS_SENSE_Get())
    {
        retVal = DRV_USB_VBUS_LEVEL_VALID;
    }
	return (retVal);

}

const DRV_USBHSV1_INIT drvUSBInit =
{
    /* Interrupt Source for USB module */
    .interruptSource = USBHS_IRQn,

    /* System module initialization */
    .moduleInit = {0},

    /* USB Controller to operate as USB Device */
    .operationMode = DRV_USBHSV1_OPMODE_DEVICE,

    /* To operate in USB Normal Mode */
    .operationSpeed = DRV_USBHSV1_DEVICE_SPEEDCONF_NORMAL,

    /* Identifies peripheral (PLIB-level) ID */
    .usbID = USBHS_REGS,
	
    /* Function to check for VBUS */
    .vbusComparator = DRV_USBHSV1_VBUS_Comparator
};




// *****************************************************************************
// *****************************************************************************
// Section: System Initialization
// *****************************************************************************
// *****************************************************************************
// <editor-fold defaultstate="collapsed" desc="SYS_TIME Initialization Data">

const SYS_TIME_PLIB_INTERFACE sysTimePlibAPI = {
    .timerCallbackSet = (SYS_TIME_PLIB_CALLBACK_REGISTER)TC1_CH0_TimerCallbackRegister,
    .timerStart = (SYS_TIME_PLIB_START)TC1_CH0_TimerStart,
    .timerStop = (SYS_TIME_PLIB_STOP)TC1_CH0_TimerStop ,
    .timerFrequencyGet = (SYS_TIME_PLIB_FREQUENCY_GET)TC1_CH0_TimerFrequencyGet,
    .timerPeriodSet = (SYS_TIME_PLIB_PERIOD_SET)TC1_CH0_TimerPeriodSet,
    .timerCompareSet = (SYS_TIME_PLIB_COMPARE_SET)TC1_CH0_TimerCompareSet,
    .timerCounterGet = (SYS_TIME_PLIB_COUNTER_GET)TC1_CH0_TimerCounterGet,
};

const SYS_TIME_INIT sysTimeInitData =
{
    .timePlib = &sysTimePlibAPI,
    .hwTimerIntNum = TC1_CH0_IRQn,
};

// </editor-fold>



// *****************************************************************************
// *****************************************************************************
// Section: Local initialization functions
// *****************************************************************************
// *****************************************************************************

/*******************************************************************************
  Function:
    void STDIO_BufferModeSet ( void )

  Summary:
    Sets the buffering mode for stdin and stdout

  Remarks:
 ********************************************************************************/
static void STDIO_BufferModeSet(void)
{

    /* Make stdin unbuffered */
    setbuf(stdin, NULL);

    /* Make stdout unbuffered */
    setbuf(stdout, NULL);
}




/*******************************************************************************
  Function:
    void SYS_Initialize ( void *data )

  Summary:
    Initializes the board, services, drivers, application and other modules.

  Remarks:
 */

void SYS_Initialize ( void* data )
{


    EFC_Initialize();
    STDIO_BufferModeSet();


  
    CLOCK_Initialize();
	PIO_Initialize();



	RSWDT_REGS->RSWDT_MR = RSWDT_MR_WDDIS_Msk;	// Disable RSWDT 

	WDT_REGS->WDT_MR = WDT_MR_WDDIS_Msk; 		// Disable WDT 

    PWM0_Initialize();

	DACC_Initialize();

  

 
    TC1_CH0_TimerInitialize(); 
    TC1_CH1_TimerInitialize(); 
     
	RTC_Initialize();

    TC0_QuadratureInitialize();
  

 
     
    
    AFEC0_Initialize();

    QSPI_Initialize();

	UART0_Initialize();

	TWIHS0_Initialize();

    MCAN1_Initialize();


    sysObj.drvSST26 = DRV_SST26_Initialize((SYS_MODULE_INDEX)DRV_SST26_INDEX, (SYS_MODULE_INIT *)&drvSST26InitData);


    sysObj.sysTime = SYS_TIME_Initialize(SYS_TIME_INDEX_0, (SYS_MODULE_INIT *)&sysTimeInitData);


	 /* Initialize the USB device layer */
    sysObj.usbDevObject0 = USB_DEVICE_Initialize (USB_DEVICE_INDEX_0 , ( SYS_MODULE_INIT* ) & usbDevInitData);
	
	

	/* Initialize USB Driver */ 
    sysObj.drvUSBHSV1Object = DRV_USBHSV1_Initialize(DRV_USBHSV1_INDEX_0, (SYS_MODULE_INIT *) &drvUSBInit);	




    NVIC_Initialize();

}


/*******************************************************************************
 End of File
*/
