bemcgarvey/SAMduino/firmware/FullDemo/firmware/src/quadrature.h

/* 
 * File:   quadrature.h
 * Author: bemcg
 *
 * Created on December 8, 2021, 9:58 AM
 */

#ifndef QUADRATURE_H
#define	QUADRATURE_H

#ifdef	__cplusplus
extern "C" {
#endif

    void quadratureMenu(void);


#ifdef	__cplusplus
}
#endif

#endif	/* QUADRATURE_H */
