bemcgarvey/SAMduino/firmware/FullDemo/firmware/src/pwm_menu.h

/* 
 * File:   pwm_menu.h
 * Author: bemcg
 *
 * Created on November 26, 2021, 10:36 AM
 */

#ifndef PWM_MENU_H
#define	PWM_MENU_H

#ifdef	__cplusplus
extern "C" {
#endif

void pwmMenu(void);

#ifdef	__cplusplus
}
#endif

#endif	/* PWM_MENU_H */
