bemcgarvey/SAMduino/firmware/FullDemo/firmware/src/analog.h

/* 
 * File:   analog.h
 * Author: bemcg
 *
 * Created on November 22, 2021, 3:23 PM
 */

#ifndef ANALOG_H
#define	ANALOG_H

#ifdef	__cplusplus
extern "C" {
#endif

    void analogMenu(void);

#ifdef	__cplusplus
}
#endif

#endif	/* ANALOG_H */
