bemcgarvey/SAMduino/firmware/FullDemo/firmware/src/rtc_menu.h

/* 
 * File:   rtc.h
 * Author: bemcg
 *
 * Created on November 22, 2021, 10:30 AM
 */

#ifndef RTC_MENU_H
#define	RTC_MENU_H

#ifdef	__cplusplus
extern "C" {
#endif

    void rtcMenu(void);

#ifdef	__cplusplus
}
#endif

#endif	/* RTC_H */
