bemcgarvey/SAMduino/firmware/FullDemo/firmware/src/twi.h

/* 
 * File:   twi.h
 * Author: bemcg
 *
 * Created on November 21, 2021, 4:41 PM
 */

#ifndef TWI_H
#define	TWI_H

#ifdef	__cplusplus
extern "C" {
#endif

    void twiMenu(void);


#ifdef	__cplusplus
}
#endif

#endif	/* TWI_H */
