bemcgarvey/SAMduino/firmware/FullDemo/firmware/src/can.h

/* 
 * File:   can.h
 * Author: bemcg
 *
 * Created on November 19, 2021, 8:18 PM
 */

#ifndef CAN_H
#define	CAN_H

#ifdef	__cplusplus
extern "C" {
#endif

    void canMenu(void);


#ifdef	__cplusplus
}
#endif

#endif	/* CAN_H */
