bemcgarvey/SAMduino/firmware/FullDemo/firmware/src/flash.h

/* 
 * File:   flash.h
 * Author: bemcg
 *
 * Created on November 19, 2021, 3:16 PM
 */

#ifndef FLASH_H
#define	FLASH_H

#ifdef	__cplusplus
extern "C" {
#endif

    void flashMenu(void);

#ifdef	__cplusplus
}
#endif

#endif	/* FLASH_H */
